guidosch/bikecounter/hardware/PCB/LogicLayer/BikeCounter_LogicLayer_v0.1_r1_p2.png

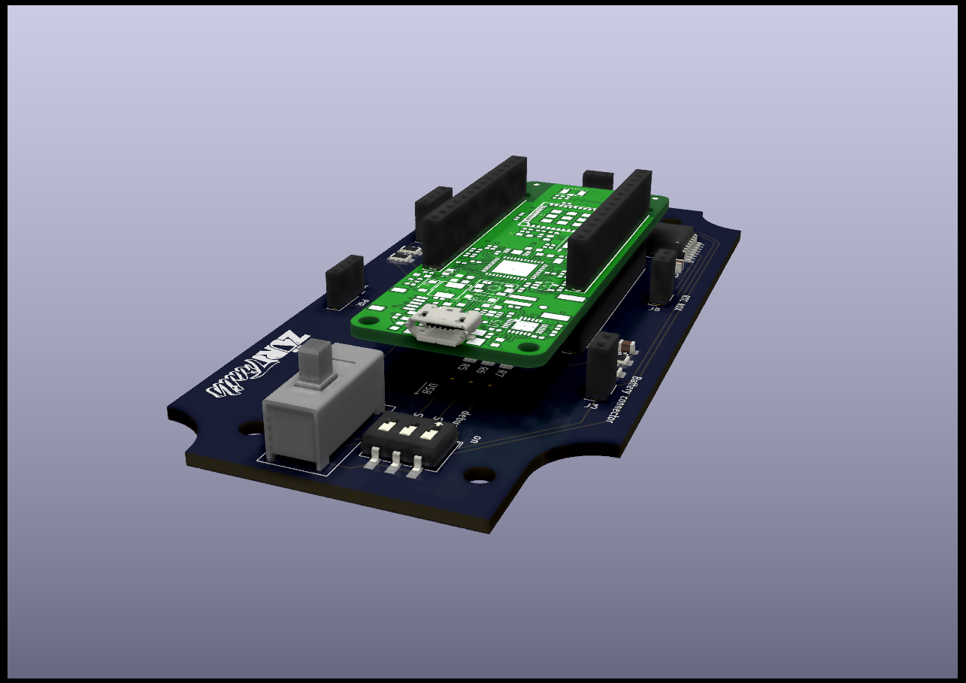
hardware/PCB/LogicLayer/BikeCounter_LogicLayer_v0.1_r1_p2.png
