guidosch/bikecounter/software/BikeCounterPro/src/timerSchedule/date.h

#ifndef DATE_H
#define DATE_H

// The MIT License (MIT)
//
// Copyright (c) 2015, 2016, 2017 Howard Hinnant
// Copyright (c) 2016 Adrian Colomitchi
// Copyright (c) 2017 Florian Dang
// Copyright (c) 2017 Paul Thompson
// Copyright (c) 2018, 2019 Tomasz Kamiński
// Copyright (c) 2019 Jiangang Zhuang
//
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
// Our apologies.  When the previous paragraph was written, lowercase had not yet
// been invented (that would involve another several millennia of evolution).
// We did not mean to shout.

#ifndef HAS_STRING_VIEW
#  if __cplusplus >= 201703 || (defined(_MSVC_LANG) && _MSVC_LANG >= 201703L)
#    define HAS_STRING_VIEW 1
#  else
#    define HAS_STRING_VIEW 0
#  endif
#endif  // HAS_STRING_VIEW

#include <cassert>
#include <algorithm>
#include <cctype>
#include <chrono>
#include <climits>
#include <cmath>
#include <cstddef>
#include <cstdint>
#include <cstdlib>
#include <ctime>
#include <ios>
#include <istream>
#include <iterator>
#include <limits>
#include <locale>
#include <memory>
#include <ostream>
#include <ratio>
#include <sstream>
#include <stdexcept>
#include <string>
#if HAS_STRING_VIEW
# include <string_view>
#endif
#include <utility>
#include <type_traits>

#ifdef __GNUC__
# pragma GCC diagnostic push
# if __GNUC__ > 4 || (__GNUC__ == 4 && __GNUC_MINOR__ > 7)
#  pragma GCC diagnostic ignored "-Wpedantic"
# endif
# if __GNUC__ < 5
   // GCC 4.9 Bug 61489 Wrong warning with -Wmissing-field-initializers
#  pragma GCC diagnostic ignored "-Wmissing-field-initializers"
# endif
#endif

#ifdef _MSC_VER
#   pragma warning(push)
// warning C4127: conditional expression is constant
#   pragma warning(disable : 4127)
#endif

namespace date
{

    //---------------+
    // Configuration |
    //---------------+

#ifndef ONLY_C_LOCALE
#  define ONLY_C_LOCALE 0
#endif

#if defined(_MSC_VER) && (!defined(__clang__) || (_MSC_VER < 1910))
// MSVC
#  ifndef _SILENCE_CXX17_UNCAUGHT_EXCEPTION_DEPRECATION_WARNING
#    define _SILENCE_CXX17_UNCAUGHT_EXCEPTION_DEPRECATION_WARNING
#  endif
#  if _MSC_VER < 1910
//   before VS2017
#    define CONSTDATA const
#    define CONSTCD11
#    define CONSTCD14
#    define NOEXCEPT _NOEXCEPT
#  else
//   VS2017 and later
#    define CONSTDATA constexpr const
#    define CONSTCD11 constexpr
#    define CONSTCD14 constexpr
#    define NOEXCEPT noexcept
#  endif

#elif defined(__SUNPRO_CC) && __SUNPRO_CC <= 0x5150
// Oracle Developer Studio 12.6 and earlier
#  define CONSTDATA constexpr const
#  define CONSTCD11 constexpr
#  define CONSTCD14
#  define NOEXCEPT noexcept

#elif __cplusplus >= 201402
// C++14
#  define CONSTDATA constexpr const
#  define CONSTCD11 constexpr
#  define CONSTCD14 constexpr
#  define NOEXCEPT noexcept
#else
// C++11
#  define CONSTDATA constexpr const
#  define CONSTCD11 constexpr
#  define CONSTCD14
#  define NOEXCEPT noexcept
#endif

#ifndef HAS_UNCAUGHT_EXCEPTIONS
#  if __cplusplus >= 201703 || (defined(_MSVC_LANG) && _MSVC_LANG >= 201703L)
#    define HAS_UNCAUGHT_EXCEPTIONS 1
#  else
#    define HAS_UNCAUGHT_EXCEPTIONS 0
#  endif
#endif  // HAS_UNCAUGHT_EXCEPTIONS

#ifndef HAS_VOID_T
#  if __cplusplus >= 201703 || (defined(_MSVC_LANG) && _MSVC_LANG >= 201703L)
#    define HAS_VOID_T 1
#  else
#    define HAS_VOID_T 0
#  endif
#endif  // HAS_VOID_T

// Protect from Oracle sun macro
#ifdef sun
#  undef sun
#endif

// Work around for a NVCC compiler bug which causes it to fail
// to compile std::ratio_{multiply,divide} when used directly
// in the std::chrono::duration template instantiations below
    namespace detail {
        template <typename R1, typename R2>
        using ratio_multiply = decltype(std::ratio_multiply<R1, R2>{});

        template <typename R1, typename R2>
        using ratio_divide = decltype(std::ratio_divide<R1, R2>{});
    }  // namespace detail

    //-----------+
    // Interface |
    //-----------+

    // durations

    using days = std::chrono::duration
        <int, detail::ratio_multiply<std::ratio<24>, std::chrono::hours::period>>;

    using weeks = std::chrono::duration
        <int, detail::ratio_multiply<std::ratio<7>, days::period>>;

    using years = std::chrono::duration
        <int, detail::ratio_multiply<std::ratio<146097, 400>, days::period>>;

    using months = std::chrono::duration
        <int, detail::ratio_divide<years::period, std::ratio<12>>>;

    // time_point

    template <class Duration>
    using sys_time = std::chrono::time_point<std::chrono::system_clock, Duration>;

    using sys_days = sys_time<days>;
    using sys_seconds = sys_time<std::chrono::seconds>;

    struct local_t {};

    template <class Duration>
    using local_time = std::chrono::time_point<local_t, Duration>;

    using local_seconds = local_time<std::chrono::seconds>;
    using local_days = local_time<days>;

    // types

    struct last_spec
    {
        explicit last_spec() = default;
    };

    class day;
    class month;
    class year;

    class weekday;
    class weekday_indexed;
    class weekday_last;

    class month_day;
    class month_day_last;
    class month_weekday;
    class month_weekday_last;

    class year_month;

    class year_month_day;
    class year_month_day_last;
    class year_month_weekday;
    class year_month_weekday_last;

    // date composition operators

    CONSTCD11 year_month operator/(const year& y, const month& m) NOEXCEPT;
    CONSTCD11 year_month operator/(const year& y, int          m) NOEXCEPT;

    CONSTCD11 month_day operator/(const day& d, const month& m) NOEXCEPT;
    CONSTCD11 month_day operator/(const day& d, int          m) NOEXCEPT;
    CONSTCD11 month_day operator/(const month& m, const day& d) NOEXCEPT;
    CONSTCD11 month_day operator/(const month& m, int        d) NOEXCEPT;
    CONSTCD11 month_day operator/(int          m, const day& d) NOEXCEPT;

    CONSTCD11 month_day_last operator/(const month& m, last_spec) NOEXCEPT;
    CONSTCD11 month_day_last operator/(int          m, last_spec) NOEXCEPT;
    CONSTCD11 month_day_last operator/(last_spec, const month& m) NOEXCEPT;
    CONSTCD11 month_day_last operator/(last_spec, int          m) NOEXCEPT;

    CONSTCD11 month_weekday operator/(const month& m, const weekday_indexed& wdi) NOEXCEPT;
    CONSTCD11 month_weekday operator/(int          m, const weekday_indexed& wdi) NOEXCEPT;
    CONSTCD11 month_weekday operator/(const weekday_indexed& wdi, const month& m) NOEXCEPT;
    CONSTCD11 month_weekday operator/(const weekday_indexed& wdi, int          m) NOEXCEPT;

    CONSTCD11 month_weekday_last operator/(const month& m, const weekday_last& wdl) NOEXCEPT;
    CONSTCD11 month_weekday_last operator/(int          m, const weekday_last& wdl) NOEXCEPT;
    CONSTCD11 month_weekday_last operator/(const weekday_last& wdl, const month& m) NOEXCEPT;
    CONSTCD11 month_weekday_last operator/(const weekday_last& wdl, int          m) NOEXCEPT;

    CONSTCD11 year_month_day operator/(const year_month& ym, const day& d) NOEXCEPT;
    CONSTCD11 year_month_day operator/(const year_month& ym, int        d) NOEXCEPT;
    CONSTCD11 year_month_day operator/(const year& y, const month_day& md) NOEXCEPT;
    CONSTCD11 year_month_day operator/(int         y, const month_day& md) NOEXCEPT;
    CONSTCD11 year_month_day operator/(const month_day& md, const year& y) NOEXCEPT;
    CONSTCD11 year_month_day operator/(const month_day& md, int         y) NOEXCEPT;

    CONSTCD11
        year_month_day_last operator/(const year_month& ym, last_spec) NOEXCEPT;
    CONSTCD11
        year_month_day_last operator/(const year& y, const month_day_last& mdl) NOEXCEPT;
    CONSTCD11
        year_month_day_last operator/(int         y, const month_day_last& mdl) NOEXCEPT;
    CONSTCD11
        year_month_day_last operator/(const month_day_last& mdl, const year& y) NOEXCEPT;
    CONSTCD11
        year_month_day_last operator/(const month_day_last& mdl, int         y) NOEXCEPT;

    CONSTCD11
        year_month_weekday
        operator/(const year_month& ym, const weekday_indexed& wdi) NOEXCEPT;

    CONSTCD11
        year_month_weekday
        operator/(const year& y, const month_weekday& mwd) NOEXCEPT;

    CONSTCD11
        year_month_weekday
        operator/(int                y, const month_weekday& mwd) NOEXCEPT;

    CONSTCD11
        year_month_weekday
        operator/(const month_weekday& mwd, const year& y) NOEXCEPT;

    CONSTCD11
        year_month_weekday
        operator/(const month_weekday& mwd, int                  y) NOEXCEPT;

    CONSTCD11
        year_month_weekday_last
        operator/(const year_month& ym, const weekday_last& wdl) NOEXCEPT;

    CONSTCD11
        year_month_weekday_last
        operator/(const year& y, const month_weekday_last& mwdl) NOEXCEPT;

    CONSTCD11
        year_month_weekday_last
        operator/(int         y, const month_weekday_last& mwdl) NOEXCEPT;

    CONSTCD11
        year_month_weekday_last
        operator/(const month_weekday_last& mwdl, const year& y) NOEXCEPT;

    CONSTCD11
        year_month_weekday_last
        operator/(const month_weekday_last& mwdl, int         y) NOEXCEPT;

    // Detailed interface

    // day

    class day
    {
        unsigned char d_;

    public:
        day() = default;
        explicit CONSTCD11 day(unsigned d) NOEXCEPT;

        CONSTCD14 day& operator++()    NOEXCEPT;
        CONSTCD14 day  operator++(int) NOEXCEPT;
        CONSTCD14 day& operator--()    NOEXCEPT;
        CONSTCD14 day  operator--(int) NOEXCEPT;

        CONSTCD14 day& operator+=(const days& d) NOEXCEPT;
        CONSTCD14 day& operator-=(const days& d) NOEXCEPT;

        CONSTCD11 explicit operator unsigned() const NOEXCEPT;
        CONSTCD11 bool ok() const NOEXCEPT;
    };

    CONSTCD11 bool operator==(const day& x, const day& y) NOEXCEPT;
    CONSTCD11 bool operator!=(const day& x, const day& y) NOEXCEPT;
    CONSTCD11 bool operator< (const day& x, const day& y) NOEXCEPT;
    CONSTCD11 bool operator> (const day& x, const day& y) NOEXCEPT;
    CONSTCD11 bool operator<=(const day& x, const day& y) NOEXCEPT;
    CONSTCD11 bool operator>=(const day& x, const day& y) NOEXCEPT;

    CONSTCD11 day  operator+(const day& x, const days& y) NOEXCEPT;
    CONSTCD11 day  operator+(const days& x, const day& y) NOEXCEPT;
    CONSTCD11 day  operator-(const day& x, const days& y) NOEXCEPT;
    CONSTCD11 days operator-(const day& x, const day& y) NOEXCEPT;

    template<class CharT, class Traits>
    std::basic_ostream<CharT, Traits>&
        operator<<(std::basic_ostream<CharT, Traits>& os, const day& d);

    // month

    class month
    {
        unsigned char m_;

    public:
        month() = default;
        explicit CONSTCD11 month(unsigned m) NOEXCEPT;

        CONSTCD14 month& operator++()    NOEXCEPT;
        CONSTCD14 month  operator++(int) NOEXCEPT;
        CONSTCD14 month& operator--()    NOEXCEPT;
        CONSTCD14 month  operator--(int) NOEXCEPT;

        CONSTCD14 month& operator+=(const months& m) NOEXCEPT;
        CONSTCD14 month& operator-=(const months& m) NOEXCEPT;

        CONSTCD11 explicit operator unsigned() const NOEXCEPT;
        CONSTCD11 bool ok() const NOEXCEPT;
    };

    CONSTCD11 bool operator==(const month& x, const month& y) NOEXCEPT;
    CONSTCD11 bool operator!=(const month& x, const month& y) NOEXCEPT;
    CONSTCD11 bool operator< (const month& x, const month& y) NOEXCEPT;
    CONSTCD11 bool operator> (const month& x, const month& y) NOEXCEPT;
    CONSTCD11 bool operator<=(const month& x, const month& y) NOEXCEPT;
    CONSTCD11 bool operator>=(const month& x, const month& y) NOEXCEPT;

    CONSTCD14 month  operator+(const month& x, const months& y) NOEXCEPT;
    CONSTCD14 month  operator+(const months& x, const month& y) NOEXCEPT;
    CONSTCD14 month  operator-(const month& x, const months& y) NOEXCEPT;
    CONSTCD14 months operator-(const month& x, const month& y) NOEXCEPT;

    template<class CharT, class Traits>
    std::basic_ostream<CharT, Traits>&
        operator<<(std::basic_ostream<CharT, Traits>& os, const month& m);

    // year

    class year
    {
        short y_;

    public:
        year() = default;
        explicit CONSTCD11 year(int y) NOEXCEPT;

        CONSTCD14 year& operator++()    NOEXCEPT;
        CONSTCD14 year  operator++(int) NOEXCEPT;
        CONSTCD14 year& operator--()    NOEXCEPT;
        CONSTCD14 year  operator--(int) NOEXCEPT;

        CONSTCD14 year& operator+=(const years& y) NOEXCEPT;
        CONSTCD14 year& operator-=(const years& y) NOEXCEPT;

        CONSTCD11 year operator-() const NOEXCEPT;
        CONSTCD11 year operator+() const NOEXCEPT;

        CONSTCD11 bool is_leap() const NOEXCEPT;

        CONSTCD11 explicit operator int() const NOEXCEPT;
        CONSTCD11 bool ok() const NOEXCEPT;

        static CONSTCD11 year min() NOEXCEPT { return year{ -32767 }; }
        static CONSTCD11 year max() NOEXCEPT { return year{ 32767 }; }
    };

    CONSTCD11 bool operator==(const year& x, const year& y) NOEXCEPT;
    CONSTCD11 bool operator!=(const year& x, const year& y) NOEXCEPT;
    CONSTCD11 bool operator< (const year& x, const year& y) NOEXCEPT;
    CONSTCD11 bool operator> (const year& x, const year& y) NOEXCEPT;
    CONSTCD11 bool operator<=(const year& x, const year& y) NOEXCEPT;
    CONSTCD11 bool operator>=(const year& x, const year& y) NOEXCEPT;

    CONSTCD11 year  operator+(const year& x, const years& y) NOEXCEPT;
    CONSTCD11 year  operator+(const years& x, const year& y) NOEXCEPT;
    CONSTCD11 year  operator-(const year& x, const years& y) NOEXCEPT;
    CONSTCD11 years operator-(const year& x, const year& y) NOEXCEPT;

    template<class CharT, class Traits>
    std::basic_ostream<CharT, Traits>&
        operator<<(std::basic_ostream<CharT, Traits>& os, const year& y);

    // weekday

    class weekday
    {
        unsigned char wd_;
    public:
        weekday() = default;
        explicit CONSTCD11 weekday(unsigned wd) NOEXCEPT;
        CONSTCD14 weekday(const sys_days& dp) NOEXCEPT;
        CONSTCD14 explicit weekday(const local_days& dp) NOEXCEPT;

        CONSTCD14 weekday& operator++()    NOEXCEPT;
        CONSTCD14 weekday  operator++(int) NOEXCEPT;
        CONSTCD14 weekday& operator--()    NOEXCEPT;
        CONSTCD14 weekday  operator--(int) NOEXCEPT;

        CONSTCD14 weekday& operator+=(const days& d) NOEXCEPT;
        CONSTCD14 weekday& operator-=(const days& d) NOEXCEPT;

        CONSTCD11 bool ok() const NOEXCEPT;

        CONSTCD11 unsigned c_encoding() const NOEXCEPT;
        CONSTCD11 unsigned iso_encoding() const NOEXCEPT;

        CONSTCD11 weekday_indexed operator[](unsigned index) const NOEXCEPT;
        CONSTCD11 weekday_last    operator[](last_spec)      const NOEXCEPT;

    private:
        static CONSTCD14 unsigned char weekday_from_days(int z) NOEXCEPT;

        friend CONSTCD11 bool operator==(const weekday& x, const weekday& y) NOEXCEPT;
        friend CONSTCD14 days operator-(const weekday& x, const weekday& y) NOEXCEPT;
        friend CONSTCD14 weekday operator+(const weekday& x, const days& y) NOEXCEPT;
        template<class CharT, class Traits>
        friend std::basic_ostream<CharT, Traits>&
            operator<<(std::basic_ostream<CharT, Traits>& os, const weekday& wd);
        friend class weekday_indexed;
    };

    CONSTCD11 bool operator==(const weekday& x, const weekday& y) NOEXCEPT;
    CONSTCD11 bool operator!=(const weekday& x, const weekday& y) NOEXCEPT;

    CONSTCD14 weekday operator+(const weekday& x, const days& y) NOEXCEPT;
    CONSTCD14 weekday operator+(const days& x, const weekday& y) NOEXCEPT;
    CONSTCD14 weekday operator-(const weekday& x, const days& y) NOEXCEPT;
    CONSTCD14 days    operator-(const weekday& x, const weekday& y) NOEXCEPT;

    template<class CharT, class Traits>
    std::basic_ostream<CharT, Traits>&
        operator<<(std::basic_ostream<CharT, Traits>& os, const weekday& wd);

    // weekday_indexed

    class weekday_indexed
    {
        unsigned char wd_ : 4;
        unsigned char index_ : 4;

    public:
        weekday_indexed() = default;
        CONSTCD11 weekday_indexed(const date::weekday& wd, unsigned index) NOEXCEPT;

        CONSTCD11 date::weekday weekday() const NOEXCEPT;
        CONSTCD11 unsigned index() const NOEXCEPT;
        CONSTCD11 bool ok() const NOEXCEPT;
    };

    CONSTCD11 bool operator==(const weekday_indexed& x, const weekday_indexed& y) NOEXCEPT;
    CONSTCD11 bool operator!=(const weekday_indexed& x, const weekday_indexed& y) NOEXCEPT;

    template<class CharT, class Traits>
    std::basic_ostream<CharT, Traits>&
        operator<<(std::basic_ostream<CharT, Traits>& os, const weekday_indexed& wdi);

    // weekday_last

    class weekday_last
    {
        date::weekday wd_;

    public:
        explicit CONSTCD11 weekday_last(const date::weekday& wd) NOEXCEPT;

        CONSTCD11 date::weekday weekday() const NOEXCEPT;
        CONSTCD11 bool ok() const NOEXCEPT;
    };

    CONSTCD11 bool operator==(const weekday_last& x, const weekday_last& y) NOEXCEPT;
    CONSTCD11 bool operator!=(const weekday_last& x, const weekday_last& y) NOEXCEPT;

    template<class CharT, class Traits>
    std::basic_ostream<CharT, Traits>&
        operator<<(std::basic_ostream<CharT, Traits>& os, const weekday_last& wdl);

    namespace detail
    {

        struct unspecified_month_disambiguator {};

    }  // namespace detail

    // year_month

    class year_month
    {
        date::year  y_;
        date::month m_;

    public:
        year_month() = default;
        CONSTCD11 year_month(const date::year& y, const date::month& m) NOEXCEPT;

        CONSTCD11 date::year  year()  const NOEXCEPT;
        CONSTCD11 date::month month() const NOEXCEPT;

        template<class = detail::unspecified_month_disambiguator>
        CONSTCD14 year_month& operator+=(const months& dm) NOEXCEPT;
        template<class = detail::unspecified_month_disambiguator>
        CONSTCD14 year_month& operator-=(const months& dm) NOEXCEPT;
        CONSTCD14 year_month& operator+=(const years& dy) NOEXCEPT;
        CONSTCD14 year_month& operator-=(const years& dy) NOEXCEPT;

        CONSTCD11 bool ok() const NOEXCEPT;
    };

    CONSTCD11 bool operator==(const year_month& x, const year_month& y) NOEXCEPT;
    CONSTCD11 bool operator!=(const year_month& x, const year_month& y) NOEXCEPT;
    CONSTCD11 bool operator< (const year_month& x, const year_month& y) NOEXCEPT;
    CONSTCD11 bool operator> (const year_month& x, const year_month& y) NOEXCEPT;
    CONSTCD11 bool operator<=(const year_month& x, const year_month& y) NOEXCEPT;
    CONSTCD11 bool operator>=(const year_month& x, const year_month& y) NOEXCEPT;

    template<class = detail::unspecified_month_disambiguator>
    CONSTCD14 year_month operator+(const year_month& ym, const months& dm) NOEXCEPT;
    template<class = detail::unspecified_month_disambiguator>
    CONSTCD14 year_month operator+(const months& dm, const year_month& ym) NOEXCEPT;
    template<class = detail::unspecified_month_disambiguator>
    CONSTCD14 year_month operator-(const year_month& ym, const months& dm) NOEXCEPT;

    CONSTCD11 months operator-(const year_month& x, const year_month& y) NOEXCEPT;
    CONSTCD11 year_month operator+(const year_month& ym, const years& dy) NOEXCEPT;
    CONSTCD11 year_month operator+(const years& dy, const year_month& ym) NOEXCEPT;
    CONSTCD11 year_month operator-(const year_month& ym, const years& dy) NOEXCEPT;

    template<class CharT, class Traits>
    std::basic_ostream<CharT, Traits>&
        operator<<(std::basic_ostream<CharT, Traits>& os, const year_month& ym);

    // month_day

    class month_day
    {
        date::month m_;
        date::day   d_;

    public:
        month_day() = default;
        CONSTCD11 month_day(const date::month& m, const date::day& d) NOEXCEPT;

        CONSTCD11 date::month month() const NOEXCEPT;
        CONSTCD11 date::day   day() const NOEXCEPT;

        CONSTCD14 bool ok() const NOEXCEPT;
    };

    CONSTCD11 bool operator==(const month_day& x, const month_day& y) NOEXCEPT;
    CONSTCD11 bool operator!=(const month_day& x, const month_day& y) NOEXCEPT;
    CONSTCD11 bool operator< (const month_day& x, const month_day& y) NOEXCEPT;
    CONSTCD11 bool operator> (const month_day& x, const month_day& y) NOEXCEPT;
    CONSTCD11 bool operator<=(const month_day& x, const month_day& y) NOEXCEPT;
    CONSTCD11 bool operator>=(const month_day& x, const month_day& y) NOEXCEPT;

    template<class CharT, class Traits>
    std::basic_ostream<CharT, Traits>&
        operator<<(std::basic_ostream<CharT, Traits>& os, const month_day& md);

    // month_day_last

    class month_day_last
    {
        date::month m_;

    public:
        CONSTCD11 explicit month_day_last(const date::month& m) NOEXCEPT;

        CONSTCD11 date::month month() const NOEXCEPT;
        CONSTCD11 bool ok() const NOEXCEPT;
    };

    CONSTCD11 bool operator==(const month_day_last& x, const month_day_last& y) NOEXCEPT;
    CONSTCD11 bool operator!=(const month_day_last& x, const month_day_last& y) NOEXCEPT;
    CONSTCD11 bool operator< (const month_day_last& x, const month_day_last& y) NOEXCEPT;
    CONSTCD11 bool operator> (const month_day_last& x, const month_day_last& y) NOEXCEPT;
    CONSTCD11 bool operator<=(const month_day_last& x, const month_day_last& y) NOEXCEPT;
    CONSTCD11 bool operator>=(const month_day_last& x, const month_day_last& y) NOEXCEPT;

    template<class CharT, class Traits>
    std::basic_ostream<CharT, Traits>&
        operator<<(std::basic_ostream<CharT, Traits>& os, const month_day_last& mdl);

    // month_weekday

    class month_weekday
    {
        date::month           m_;
        date::weekday_indexed wdi_;
    public:
        CONSTCD11 month_weekday(const date::month& m,
            const date::weekday_indexed& wdi) NOEXCEPT;

        CONSTCD11 date::month           month()           const NOEXCEPT;
        CONSTCD11 date::weekday_indexed weekday_indexed() const NOEXCEPT;

        CONSTCD11 bool ok() const NOEXCEPT;
    };

    CONSTCD11 bool operator==(const month_weekday& x, const month_weekday& y) NOEXCEPT;
    CONSTCD11 bool operator!=(const month_weekday& x, const month_weekday& y) NOEXCEPT;

    template<class CharT, class Traits>
    std::basic_ostream<CharT, Traits>&
        operator<<(std::basic_ostream<CharT, Traits>& os, const month_weekday& mwd);

    // month_weekday_last

    class month_weekday_last
    {
        date::month        m_;
        date::weekday_last wdl_;

    public:
        CONSTCD11 month_weekday_last(const date::month& m,
            const date::weekday_last& wd) NOEXCEPT;

        CONSTCD11 date::month        month()        const NOEXCEPT;
        CONSTCD11 date::weekday_last weekday_last() const NOEXCEPT;

        CONSTCD11 bool ok() const NOEXCEPT;
    };

    CONSTCD11
        bool operator==(const month_weekday_last& x, const month_weekday_last& y) NOEXCEPT;
    CONSTCD11
        bool operator!=(const month_weekday_last& x, const month_weekday_last& y) NOEXCEPT;

    template<class CharT, class Traits>
    std::basic_ostream<CharT, Traits>&
        operator<<(std::basic_ostream<CharT, Traits>& os, const month_weekday_last& mwdl);

    // class year_month_day

    class year_month_day
    {
        date::year  y_;
        date::month m_;
        date::day   d_;

    public:
        year_month_day() = default;
        CONSTCD11 year_month_day(const date::year& y, const date::month& m,
            const date::day& d) NOEXCEPT;
        CONSTCD14 year_month_day(const year_month_day_last& ymdl) NOEXCEPT;

        CONSTCD14 year_month_day(sys_days dp) NOEXCEPT;
        CONSTCD14 explicit year_month_day(local_days dp) NOEXCEPT;

        template<class = detail::unspecified_month_disambiguator>
        CONSTCD14 year_month_day& operator+=(const months& m) NOEXCEPT;
        template<class = detail::unspecified_month_disambiguator>
        CONSTCD14 year_month_day& operator-=(const months& m) NOEXCEPT;
        CONSTCD14 year_month_day& operator+=(const years& y)  NOEXCEPT;
        CONSTCD14 year_month_day& operator-=(const years& y)  NOEXCEPT;

        CONSTCD11 date::year  year()  const NOEXCEPT;
        CONSTCD11 date::month month() const NOEXCEPT;
        CONSTCD11 date::day   day()   const NOEXCEPT;

        CONSTCD14 operator sys_days() const NOEXCEPT;
        CONSTCD14 explicit operator local_days() const NOEXCEPT;
        CONSTCD14 bool ok() const NOEXCEPT;

    private:
        static CONSTCD14 year_month_day from_days(days dp) NOEXCEPT;
        CONSTCD14 days to_days() const NOEXCEPT;
    };

    CONSTCD11 bool operator==(const year_month_day& x, const year_month_day& y) NOEXCEPT;
    CONSTCD11 bool operator!=(const year_month_day& x, const year_month_day& y) NOEXCEPT;
    CONSTCD11 bool operator< (const year_month_day& x, const year_month_day& y) NOEXCEPT;
    CONSTCD11 bool operator> (const year_month_day& x, const year_month_day& y) NOEXCEPT;
    CONSTCD11 bool operator<=(const year_month_day& x, const year_month_day& y) NOEXCEPT;
    CONSTCD11 bool operator>=(const year_month_day& x, const year_month_day& y) NOEXCEPT;

    template<class = detail::unspecified_month_disambiguator>
    CONSTCD14 year_month_day operator+(const year_month_day& ymd, const months& dm) NOEXCEPT;
    template<class = detail::unspecified_month_disambiguator>
    CONSTCD14 year_month_day operator+(const months& dm, const year_month_day& ymd) NOEXCEPT;
    template<class = detail::unspecified_month_disambiguator>
    CONSTCD14 year_month_day operator-(const year_month_day& ymd, const months& dm) NOEXCEPT;
    CONSTCD11 year_month_day operator+(const year_month_day& ymd, const years& dy)  NOEXCEPT;
    CONSTCD11 year_month_day operator+(const years& dy, const year_month_day& ymd)  NOEXCEPT;
    CONSTCD11 year_month_day operator-(const year_month_day& ymd, const years& dy)  NOEXCEPT;

    template<class CharT, class Traits>
    std::basic_ostream<CharT, Traits>&
        operator<<(std::basic_ostream<CharT, Traits>& os, const year_month_day& ymd);

    // year_month_day_last

    class year_month_day_last
    {
        date::year           y_;
        date::month_day_last mdl_;

    public:
        CONSTCD11 year_month_day_last(const date::year& y,
            const date::month_day_last& mdl) NOEXCEPT;

        template<class = detail::unspecified_month_disambiguator>
        CONSTCD14 year_month_day_last& operator+=(const months& m) NOEXCEPT;
        template<class = detail::unspecified_month_disambiguator>
        CONSTCD14 year_month_day_last& operator-=(const months& m) NOEXCEPT;
        CONSTCD14 year_month_day_last& operator+=(const years& y)  NOEXCEPT;
        CONSTCD14 year_month_day_last& operator-=(const years& y)  NOEXCEPT;

        CONSTCD11 date::year           year()           const NOEXCEPT;
        CONSTCD11 date::month          month()          const NOEXCEPT;
        CONSTCD11 date::month_day_last month_day_last() const NOEXCEPT;
        CONSTCD14 date::day            day()            const NOEXCEPT;

        CONSTCD14 operator sys_days() const NOEXCEPT;
        CONSTCD14 explicit operator local_days() const NOEXCEPT;
        CONSTCD11 bool ok() const NOEXCEPT;
    };

    CONSTCD11
        bool operator==(const year_month_day_last& x, const year_month_day_last& y) NOEXCEPT;
    CONSTCD11
        bool operator!=(const year_month_day_last& x, const year_month_day_last& y) NOEXCEPT;
    CONSTCD11
        bool operator< (const year_month_day_last& x, const year_month_day_last& y) NOEXCEPT;
    CONSTCD11
        bool operator> (const year_month_day_last& x, const year_month_day_last& y) NOEXCEPT;
    CONSTCD11
        bool operator<=(const year_month_day_last& x, const year_month_day_last& y) NOEXCEPT;
    CONSTCD11
        bool operator>=(const year_month_day_last& x, const year_month_day_last& y) NOEXCEPT;

    template<class = detail::unspecified_month_disambiguator>
    CONSTCD14
        year_month_day_last
        operator+(const year_month_day_last& ymdl, const months& dm) NOEXCEPT;

    template<class = detail::unspecified_month_disambiguator>
    CONSTCD14
        year_month_day_last
        operator+(const months& dm, const year_month_day_last& ymdl) NOEXCEPT;

    CONSTCD11
        year_month_day_last
        operator+(const year_month_day_last& ymdl, const years& dy) NOEXCEPT;

    CONSTCD11
        year_month_day_last
        operator+(const years& dy, const year_month_day_last& ymdl) NOEXCEPT;

    template<class = detail::unspecified_month_disambiguator>
    CONSTCD14
        year_month_day_last
        operator-(const year_month_day_last& ymdl, const months& dm) NOEXCEPT;

    CONSTCD11
        year_month_day_last
        operator-(const year_month_day_last& ymdl, const years& dy) NOEXCEPT;

    template<class CharT, class Traits>
    std::basic_ostream<CharT, Traits>&
        operator<<(std::basic_ostream<CharT, Traits>& os, const year_month_day_last& ymdl);

    // year_month_weekday

    class year_month_weekday
    {
        date::year            y_;
        date::month           m_;
        date::weekday_indexed wdi_;

    public:
        year_month_weekday() = default;
        CONSTCD11 year_month_weekday(const date::year& y, const date::month& m,
            const date::weekday_indexed& wdi) NOEXCEPT;
        CONSTCD14 year_month_weekday(const sys_days& dp) NOEXCEPT;
        CONSTCD14 explicit year_month_weekday(const local_days& dp) NOEXCEPT;

        template<class = detail::unspecified_month_disambiguator>
        CONSTCD14 year_month_weekday& operator+=(const months& m) NOEXCEPT;
        template<class = detail::unspecified_month_disambiguator>
        CONSTCD14 year_month_weekday& operator-=(const months& m) NOEXCEPT;
        CONSTCD14 year_month_weekday& operator+=(const years& y)  NOEXCEPT;
        CONSTCD14 year_month_weekday& operator-=(const years& y)  NOEXCEPT;

        CONSTCD11 date::year year() const NOEXCEPT;
        CONSTCD11 date::month month() const NOEXCEPT;
        CONSTCD11 date::weekday weekday() const NOEXCEPT;
        CONSTCD11 unsigned index() const NOEXCEPT;
        CONSTCD11 date::weekday_indexed weekday_indexed() const NOEXCEPT;

        CONSTCD14 operator sys_days() const NOEXCEPT;
        CONSTCD14 explicit operator local_days() const NOEXCEPT;
        CONSTCD14 bool ok() const NOEXCEPT;

    private:
        static CONSTCD14 year_month_weekday from_days(days dp) NOEXCEPT;
        CONSTCD14 days to_days() const NOEXCEPT;
    };

    CONSTCD11
        bool operator==(const year_month_weekday& x, const year_month_weekday& y) NOEXCEPT;
    CONSTCD11
        bool operator!=(const year_month_weekday& x, const year_month_weekday& y) NOEXCEPT;

    template<class = detail::unspecified_month_disambiguator>
    CONSTCD14
        year_month_weekday
        operator+(const year_month_weekday& ymwd, const months& dm) NOEXCEPT;

    template<class = detail::unspecified_month_disambiguator>
    CONSTCD14
        year_month_weekday
        operator+(const months& dm, const year_month_weekday& ymwd) NOEXCEPT;

    CONSTCD11
        year_month_weekday
        operator+(const year_month_weekday& ymwd, const years& dy) NOEXCEPT;

    CONSTCD11
        year_month_weekday
        operator+(const years& dy, const year_month_weekday& ymwd) NOEXCEPT;

    template<class = detail::unspecified_month_disambiguator>
    CONSTCD14
        year_month_weekday
        operator-(const year_month_weekday& ymwd, const months& dm) NOEXCEPT;

    CONSTCD11
        year_month_weekday
        operator-(const year_month_weekday& ymwd, const years& dy) NOEXCEPT;

    template<class CharT, class Traits>
    std::basic_ostream<CharT, Traits>&
        operator<<(std::basic_ostream<CharT, Traits>& os, const year_month_weekday& ymwdi);

    // year_month_weekday_last

    class year_month_weekday_last
    {
        date::year y_;
        date::month m_;
        date::weekday_last wdl_;

    public:
        CONSTCD11 year_month_weekday_last(const date::year& y, const date::month& m,
            const date::weekday_last& wdl) NOEXCEPT;

        template<class = detail::unspecified_month_disambiguator>
        CONSTCD14 year_month_weekday_last& operator+=(const months& m) NOEXCEPT;
        template<class = detail::unspecified_month_disambiguator>
        CONSTCD14 year_month_weekday_last& operator-=(const months& m) NOEXCEPT;
        CONSTCD14 year_month_weekday_last& operator+=(const years& y) NOEXCEPT;
        CONSTCD14 year_month_weekday_last& operator-=(const years& y) NOEXCEPT;

        CONSTCD11 date::year year() const NOEXCEPT;
        CONSTCD11 date::month month() const NOEXCEPT;
        CONSTCD11 date::weekday weekday() const NOEXCEPT;
        CONSTCD11 date::weekday_last weekday_last() const NOEXCEPT;

        CONSTCD14 operator sys_days() const NOEXCEPT;
        CONSTCD14 explicit operator local_days() const NOEXCEPT;
        CONSTCD11 bool ok() const NOEXCEPT;

    private:
        CONSTCD14 days to_days() const NOEXCEPT;
    };

    CONSTCD11
        bool
        operator==(const year_month_weekday_last& x, const year_month_weekday_last& y) NOEXCEPT;

    CONSTCD11
        bool
        operator!=(const year_month_weekday_last& x, const year_month_weekday_last& y) NOEXCEPT;

    template<class = detail::unspecified_month_disambiguator>
    CONSTCD14
        year_month_weekday_last
        operator+(const year_month_weekday_last& ymwdl, const months& dm) NOEXCEPT;

    template<class = detail::unspecified_month_disambiguator>
    CONSTCD14
        year_month_weekday_last
        operator+(const months& dm, const year_month_weekday_last& ymwdl) NOEXCEPT;

    CONSTCD11
        year_month_weekday_last
        operator+(const year_month_weekday_last& ymwdl, const years& dy) NOEXCEPT;

    CONSTCD11
        year_month_weekday_last
        operator+(const years& dy, const year_month_weekday_last& ymwdl) NOEXCEPT;

    template<class = detail::unspecified_month_disambiguator>
    CONSTCD14
        year_month_weekday_last
        operator-(const year_month_weekday_last& ymwdl, const months& dm) NOEXCEPT;

    CONSTCD11
        year_month_weekday_last
        operator-(const year_month_weekday_last& ymwdl, const years& dy) NOEXCEPT;

    template<class CharT, class Traits>
    std::basic_ostream<CharT, Traits>&
        operator<<(std::basic_ostream<CharT, Traits>& os, const year_month_weekday_last& ymwdl);

#if !defined(_MSC_VER) || (_MSC_VER >= 1900)
    inline namespace literals
    {

        CONSTCD11 date::day  operator "" _d(unsigned long long d) NOEXCEPT;
        CONSTCD11 date::year operator "" _y(unsigned long long y) NOEXCEPT;

    }  // inline namespace literals
#endif // !defined(_MSC_VER) || (_MSC_VER >= 1900)

// CONSTDATA date::month January{1};
// CONSTDATA date::month February{2};
// CONSTDATA date::month March{3};
// CONSTDATA date::month April{4};
// CONSTDATA date::month May{5};
// CONSTDATA date::month June{6};
// CONSTDATA date::month July{7};
// CONSTDATA date::month August{8};
// CONSTDATA date::month September{9};
// CONSTDATA date::month October{10};
// CONSTDATA date::month November{11};
// CONSTDATA date::month December{12};
//
// CONSTDATA date::weekday Sunday{0u};
// CONSTDATA date::weekday Monday{1u};
// CONSTDATA date::weekday Tuesday{2u};
// CONSTDATA date::weekday Wednesday{3u};
// CONSTDATA date::weekday Thursday{4u};
// CONSTDATA date::weekday Friday{5u};
// CONSTDATA date::weekday Saturday{6u};

#if HAS_VOID_T

    template <class T, class = std::void_t<>>
    struct is_clock
        : std::false_type
    {};

    template <class T>
    struct is_clock<T, std::void_t<decltype(T::now()), typename T::rep, typename T::period,
        typename T::duration, typename T::time_point,
        decltype(T::is_steady)>>
        : std::true_type
    {};

    template<class T> inline constexpr bool is_clock_v = is_clock<T>::value;

#endif  // HAS_VOID_T

    //----------------+
    // Implementation |
    //----------------+

    // utilities
    namespace detail {

        template<class CharT, class Traits = std::char_traits<CharT>>
        class save_istream
        {
        protected:
            std::basic_ios<CharT, Traits>& is_;
            CharT fill_;
            std::ios::fmtflags flags_;
            std::streamsize precision_;
            std::streamsize width_;
            std::basic_ostream<CharT, Traits>* tie_;
            std::locale loc_;

        public:
            ~save_istream()
            {
                is_.fill(fill_);
                is_.flags(flags_);
                is_.precision(precision_);
                is_.width(width_);
                is_.imbue(loc_);
                is_.tie(tie_);
            }

            save_istream(const save_istream&) = delete;
            save_istream& operator=(const save_istream&) = delete;

            explicit save_istream(std::basic_ios<CharT, Traits>& is)
                : is_(is)
                , fill_(is.fill())
                , flags_(is.flags())
                , precision_(is.precision())
                , width_(is.width(0))
                , tie_(is.tie(nullptr))
                , loc_(is.getloc())
            {
                if (tie_ != nullptr)
                    tie_->flush();
            }
        };

        template<class CharT, class Traits = std::char_traits<CharT>>
        class save_ostream
            : private save_istream<CharT, Traits>
        {
        public:
            ~save_ostream()
            {
                if ((this->flags_ & std::ios::unitbuf) &&
#if HAS_UNCAUGHT_EXCEPTIONS
                    std::uncaught_exceptions() == 0 &&
#else
                    !std::uncaught_exception() &&
#endif
                    this->is_.good())
                    this->is_.rdbuf()->pubsync();
            }

            save_ostream(const save_ostream&) = delete;
            save_ostream& operator=(const save_ostream&) = delete;

            explicit save_ostream(std::basic_ios<CharT, Traits>& os)
                : save_istream<CharT, Traits>(os)
            {
            }
        };

        template <class T>
        struct choose_trunc_type
        {
            static const int digits = std::numeric_limits<T>::digits;
            using type = typename std::conditional
                <
                digits < 32,
                std::int32_t,
                typename std::conditional
                <
                digits < 64,
                std::int64_t,
#ifdef __SIZEOF_INT128__
                __int128
#else
                std::int64_t
#endif
                >::type
                >::type;
        };

        template <class T>
        CONSTCD11
            inline
            typename std::enable_if
            <
            !std::chrono::treat_as_floating_point<T>::value,
            T
            >::type
            trunc(T t) NOEXCEPT
        {
            return t;
        }

        template <class T>
        CONSTCD14
            inline
            typename std::enable_if
            <
            std::chrono::treat_as_floating_point<T>::value,
            T
            >::type
            trunc(T t) NOEXCEPT
        {
            using std::numeric_limits;
            using I = typename choose_trunc_type<T>::type;
            CONSTDATA auto digits = numeric_limits<T>::digits;
            static_assert(digits < numeric_limits<I>::digits, "");
            CONSTDATA auto max = I{ 1 } << (digits - 1);
            CONSTDATA auto min = -max;
            const auto negative = t < T{ 0 };
            if (min <= t && t <= max && t != 0 && t == t)
            {
                t = static_cast<T>(static_cast<I>(t));
                if (t == 0 && negative)
                    t = -t;
            }
            return t;
        }

        template <std::intmax_t Xp, std::intmax_t Yp>
        struct static_gcd
        {
            static const std::intmax_t value = static_gcd<Yp, Xp% Yp>::value;
        };

        template <std::intmax_t Xp>
        struct static_gcd<Xp, 0>
        {
            static const std::intmax_t value = Xp;
        };

        template <>
        struct static_gcd<0, 0>
        {
            static const std::intmax_t value = 1;
        };

        template <class R1, class R2>
        struct no_overflow
        {
        private:
            static const std::intmax_t gcd_n1_n2 = static_gcd<R1::num, R2::num>::value;
            static const std::intmax_t gcd_d1_d2 = static_gcd<R1::den, R2::den>::value;
            static const std::intmax_t n1 = R1::num / gcd_n1_n2;
            static const std::intmax_t d1 = R1::den / gcd_d1_d2;
            static const std::intmax_t n2 = R2::num / gcd_n1_n2;
            static const std::intmax_t d2 = R2::den / gcd_d1_d2;
#ifdef __cpp_constexpr
            static const std::intmax_t max = std::numeric_limits<std::intmax_t>::max();
#else
            static const std::intmax_t max = LLONG_MAX;
#endif

            template <std::intmax_t Xp, std::intmax_t Yp, bool overflow>
            struct mul    // overflow == false
            {
                static const std::intmax_t value = Xp * Yp;
            };

            template <std::intmax_t Xp, std::intmax_t Yp>
            struct mul<Xp, Yp, true>
            {
                static const std::intmax_t value = 1;
            };

        public:
            static const bool value = (n1 <= max / d2) && (n2 <= max / d1);
            typedef std::ratio<mul<n1, d2, !value>::value,
                mul<n2, d1, !value>::value> type;
        };

    }  // detail

    // trunc towards zero
    template <class To, class Rep, class Period>
    CONSTCD11
        inline
        typename std::enable_if
        <
        detail::no_overflow<Period, typename To::period>::value,
        To
        >::type
        trunc(const std::chrono::duration<Rep, Period>& d)
    {
        return To{ detail::trunc(std::chrono::duration_cast<To>(d).count()) };
    }

    template <class To, class Rep, class Period>
    CONSTCD11
        inline
        typename std::enable_if
        <
        !detail::no_overflow<Period, typename To::period>::value,
        To
        >::type
        trunc(const std::chrono::duration<Rep, Period>& d)
    {
        using std::chrono::duration_cast;
        using std::chrono::duration;
        using rep = typename std::common_type<Rep, typename To::rep>::type;
        return To{ detail::trunc(duration_cast<To>(duration_cast<duration<rep>>(d)).count()) };
    }

#ifndef HAS_CHRONO_ROUNDING
#  if defined(_MSC_FULL_VER) && (_MSC_FULL_VER >= 190023918 || (_MSC_FULL_VER >= 190000000 && defined (__clang__)))
#    define HAS_CHRONO_ROUNDING 1
#  elif defined(__cpp_lib_chrono) && __cplusplus > 201402 && __cpp_lib_chrono >= 201510
#    define HAS_CHRONO_ROUNDING 1
#  elif defined(_LIBCPP_VERSION) && __cplusplus > 201402 && _LIBCPP_VERSION >= 3800
#    define HAS_CHRONO_ROUNDING 1
#  else
#    define HAS_CHRONO_ROUNDING 0
#  endif
#endif  // HAS_CHRONO_ROUNDING

#if HAS_CHRONO_ROUNDING == 0

    // round down
    template <class To, class Rep, class Period>
    CONSTCD14
        inline
        typename std::enable_if
        <
        detail::no_overflow<Period, typename To::period>::value,
        To
        >::type
        floor(const std::chrono::duration<Rep, Period>& d)
    {
        auto t = trunc<To>(d);
        if (t > d)
            return t - To{ 1 };
        return t;
    }

    template <class To, class Rep, class Period>
    CONSTCD14
        inline
        typename std::enable_if
        <
        !detail::no_overflow<Period, typename To::period>::value,
        To
        >::type
        floor(const std::chrono::duration<Rep, Period>& d)
    {
        using rep = typename std::common_type<Rep, typename To::rep>::type;
        return floor<To>(floor<std::chrono::duration<rep>>(d));
    }

    // round to nearest, to even on tie
    template <class To, class Rep, class Period>
    CONSTCD14
        inline
        To
        round(const std::chrono::duration<Rep, Period>& d)
    {
        auto t0 = floor<To>(d);
        auto t1 = t0 + To{ 1 };
        if (t1 == To{ 0 } && t0 < To{ 0 })
            t1 = -t1;
        auto diff0 = d - t0;
        auto diff1 = t1 - d;
        if (diff0 == diff1)
        {
            if (t0 - trunc<To>(t0 / 2) * 2 == To{ 0 })
                return t0;
            return t1;
        }
        if (diff0 < diff1)
            return t0;
        return t1;
    }

    // round up
    template <class To, class Rep, class Period>
    CONSTCD14
        inline
        To
        ceil(const std::chrono::duration<Rep, Period>& d)
    {
        auto t = trunc<To>(d);
        if (t < d)
            return t + To{ 1 };
        return t;
    }

    template <class Rep, class Period,
        class = typename std::enable_if
        <
        std::numeric_limits<Rep>::is_signed
    >::type>
        CONSTCD11
        std::chrono::duration<Rep, Period>
        date_abs(std::chrono::duration<Rep, Period> d)
    {
        return d >= d.zero() ? d : static_cast<decltype(d)>(-d);
    }

    // round down
    template <class To, class Clock, class FromDuration>
    CONSTCD11
        inline
        std::chrono::time_point<Clock, To>
        floor(const std::chrono::time_point<Clock, FromDuration>& tp)
    {
        using std::chrono::time_point;
        return time_point<Clock, To>{date::floor<To>(tp.time_since_epoch())};
    }

    // round to nearest, to even on tie
    template <class To, class Clock, class FromDuration>
    CONSTCD11
        inline
        std::chrono::time_point<Clock, To>
        round(const std::chrono::time_point<Clock, FromDuration>& tp)
    {
        using std::chrono::time_point;
        return time_point<Clock, To>{round<To>(tp.time_since_epoch())};
    }

    // round up
    template <class To, class Clock, class FromDuration>
    CONSTCD11
        inline
        std::chrono::time_point<Clock, To>
        ceil(const std::chrono::time_point<Clock, FromDuration>& tp)
    {
        using std::chrono::time_point;
        return time_point<Clock, To>{ceil<To>(tp.time_since_epoch())};
    }

#else  // HAS_CHRONO_ROUNDING == 1

    using std::chrono::floor;
    using std::chrono::ceil;
    using std::chrono::round;
    using std::chrono::abs;

#endif  // HAS_CHRONO_ROUNDING

    namespace detail
    {

        template <class To, class Rep, class Period>
        CONSTCD14
            inline
            typename std::enable_if
            <
            !std::chrono::treat_as_floating_point<typename To::rep>::value,
            To
            >::type
            round_i(const std::chrono::duration<Rep, Period>& d)
        {
            return round<To>(d);
        }

        template <class To, class Rep, class Period>
        CONSTCD14
            inline
            typename std::enable_if
            <
            std::chrono::treat_as_floating_point<typename To::rep>::value,
            To
            >::type
            round_i(const std::chrono::duration<Rep, Period>& d)
        {
            return d;
        }

        template <class To, class Clock, class FromDuration>
        CONSTCD11
            inline
            std::chrono::time_point<Clock, To>
            round_i(const std::chrono::time_point<Clock, FromDuration>& tp)
        {
            using std::chrono::time_point;
            return time_point<Clock, To>{round_i<To>(tp.time_since_epoch())};
        }

    }  // detail

    // trunc towards zero
    template <class To, class Clock, class FromDuration>
    CONSTCD11
        inline
        std::chrono::time_point<Clock, To>
        trunc(const std::chrono::time_point<Clock, FromDuration>& tp)
    {
        using std::chrono::time_point;
        return time_point<Clock, To>{trunc<To>(tp.time_since_epoch())};
    }

    // day

    CONSTCD11 inline day::day(unsigned d) NOEXCEPT : d_(static_cast<decltype(d_)>(d)) {}
    CONSTCD14 inline day& day::operator++() NOEXCEPT { ++d_; return *this; }
    CONSTCD14 inline day day::operator++(int) NOEXCEPT { auto tmp(*this); ++(*this); return tmp; }
    CONSTCD14 inline day& day::operator--() NOEXCEPT { --d_; return *this; }
    CONSTCD14 inline day day::operator--(int) NOEXCEPT { auto tmp(*this); --(*this); return tmp; }
    CONSTCD14 inline day& day::operator+=(const days& d) NOEXCEPT { *this = *this + d; return *this; }
    CONSTCD14 inline day& day::operator-=(const days& d) NOEXCEPT { *this = *this - d; return *this; }
    CONSTCD11 inline day::operator unsigned() const NOEXCEPT { return d_; }
    CONSTCD11 inline bool day::ok() const NOEXCEPT { return 1 <= d_ && d_ <= 31; }

    CONSTCD11
        inline
        bool
        operator==(const day& x, const day& y) NOEXCEPT
    {
        return static_cast<unsigned>(x) == static_cast<unsigned>(y);
    }

    CONSTCD11
        inline
        bool
        operator!=(const day& x, const day& y) NOEXCEPT
    {
        return !(x == y);
    }

    CONSTCD11
        inline
        bool
        operator<(const day& x, const day& y) NOEXCEPT
    {
        return static_cast<unsigned>(x) < static_cast<unsigned>(y);
    }

    CONSTCD11
        inline
        bool
        operator>(const day& x, const day& y) NOEXCEPT
    {
        return y < x;
    }

    CONSTCD11
        inline
        bool
        operator<=(const day& x, const day& y) NOEXCEPT
    {
        return !(y < x);
    }

    CONSTCD11
        inline
        bool
        operator>=(const day& x, const day& y) NOEXCEPT
    {
        return !(x < y);
    }

    CONSTCD11
        inline
        days
        operator-(const day& x, const day& y) NOEXCEPT
    {
        return days{ static_cast<days::rep>(static_cast<unsigned>(x)
                                         - static_cast<unsigned>(y)) };
    }

    CONSTCD11
        inline
        day
        operator+(const day& x, const days& y) NOEXCEPT
    {
        return day{ static_cast<unsigned>(x) + static_cast<unsigned>(y.count()) };
    }

    CONSTCD11
        inline
        day
        operator+(const days& x, const day& y) NOEXCEPT
    {
        return y + x;
    }

    CONSTCD11
        inline
        day
        operator-(const day& x, const days& y) NOEXCEPT
    {
        return x + -y;
    }

    namespace detail
    {

        template<class CharT, class Traits>
        std::basic_ostream<CharT, Traits>&
            low_level_fmt(std::basic_ostream<CharT, Traits>& os, const day& d)
        {
            detail::save_ostream<CharT, Traits> _(os);
            os.fill('0');
            os.flags(std::ios::dec | std::ios::right);
            os.width(2);
            os << static_cast<unsigned>(d);
            return os;
        }

    }  // namespace detail

    template<class CharT, class Traits>
    inline
        std::basic_ostream<CharT, Traits>&
        operator<<(std::basic_ostream<CharT, Traits>& os, const day& d)
    {
        detail::low_level_fmt(os, d);
        if (!d.ok())
            os << " is not a valid day";
        return os;
    }

    // month

    CONSTCD11 inline month::month(unsigned m) NOEXCEPT : m_(static_cast<decltype(m_)>(m)) {}
    CONSTCD14 inline month& month::operator++() NOEXCEPT { *this += months{ 1 }; return *this; }
    CONSTCD14 inline month month::operator++(int) NOEXCEPT { auto tmp(*this); ++(*this); return tmp; }
    CONSTCD14 inline month& month::operator--() NOEXCEPT { *this -= months{ 1 }; return *this; }
    CONSTCD14 inline month month::operator--(int) NOEXCEPT { auto tmp(*this); --(*this); return tmp; }

    CONSTCD14
        inline
        month&
        month::operator+=(const months& m) NOEXCEPT
    {
        *this = *this + m;
        return *this;
    }

    CONSTCD14
        inline
        month&
        month::operator-=(const months& m) NOEXCEPT
    {
        *this = *this - m;
        return *this;
    }

    CONSTCD11 inline month::operator unsigned() const NOEXCEPT { return m_; }
    CONSTCD11 inline bool month::ok() const NOEXCEPT { return 1 <= m_ && m_ <= 12; }

    CONSTCD11
        inline
        bool
        operator==(const month& x, const month& y) NOEXCEPT
    {
        return static_cast<unsigned>(x) == static_cast<unsigned>(y);
    }

    CONSTCD11
        inline
        bool
        operator!=(const month& x, const month& y) NOEXCEPT
    {
        return !(x == y);
    }

    CONSTCD11
        inline
        bool
        operator<(const month& x, const month& y) NOEXCEPT
    {
        return static_cast<unsigned>(x) < static_cast<unsigned>(y);
    }

    CONSTCD11
        inline
        bool
        operator>(const month& x, const month& y) NOEXCEPT
    {
        return y < x;
    }

    CONSTCD11
        inline
        bool
        operator<=(const month& x, const month& y) NOEXCEPT
    {
        return !(y < x);
    }

    CONSTCD11
        inline
        bool
        operator>=(const month& x, const month& y) NOEXCEPT
    {
        return !(x < y);
    }

    CONSTCD14
        inline
        months
        operator-(const month& x, const month& y) NOEXCEPT
    {
        auto const d = static_cast<unsigned>(x) - static_cast<unsigned>(y);
        return months(d <= 11 ? d : d + 12);
    }

    CONSTCD14
        inline
        month
        operator+(const month& x, const months& y) NOEXCEPT
    {
        auto const mu = static_cast<long long>(static_cast<unsigned>(x)) + y.count() - 1;
        auto const yr = (mu >= 0 ? mu : mu - 11) / 12;
        return month{ static_cast<unsigned>(mu - yr * 12 + 1) };
    }

    CONSTCD14
        inline
        month
        operator+(const months& x, const month& y) NOEXCEPT
    {
        return y + x;
    }

    CONSTCD14
        inline
        month
        operator-(const month& x, const months& y) NOEXCEPT
    {
        return x + -y;
    }

    namespace detail
    {

        template<class CharT, class Traits>
        std::basic_ostream<CharT, Traits>&
            low_level_fmt(std::basic_ostream<CharT, Traits>& os, const month& m)
        {
            if (m.ok())
            {
                CharT fmt[] = { '%', 'b', 0 };
                os << format(os.getloc(), fmt, m);
            }
            else
                os << static_cast<unsigned>(m);
            return os;
        }

    }  // namespace detail

    template<class CharT, class Traits>
    inline
        std::basic_ostream<CharT, Traits>&
        operator<<(std::basic_ostream<CharT, Traits>& os, const month& m)
    {
        detail::low_level_fmt(os, m);
        if (!m.ok())
            os << " is not a valid month";
        return os;
    }

    // year

    CONSTCD11 inline year::year(int y) NOEXCEPT : y_(static_cast<decltype(y_)>(y)) {}
    CONSTCD14 inline year& year::operator++() NOEXCEPT { ++y_; return *this; }
    CONSTCD14 inline year year::operator++(int) NOEXCEPT { auto tmp(*this); ++(*this); return tmp; }
    CONSTCD14 inline year& year::operator--() NOEXCEPT { --y_; return *this; }
    CONSTCD14 inline year year::operator--(int) NOEXCEPT { auto tmp(*this); --(*this); return tmp; }
    CONSTCD14 inline year& year::operator+=(const years& y) NOEXCEPT { *this = *this + y; return *this; }
    CONSTCD14 inline year& year::operator-=(const years& y) NOEXCEPT { *this = *this - y; return *this; }
    CONSTCD11 inline year year::operator-() const NOEXCEPT { return year{ -y_ }; }
    CONSTCD11 inline year year::operator+() const NOEXCEPT { return *this; }

    CONSTCD11
        inline
        bool
        year::is_leap() const NOEXCEPT
    {
        return y_ % 4 == 0 && (y_ % 100 != 0 || y_ % 400 == 0);
    }

    CONSTCD11 inline year::operator int() const NOEXCEPT { return y_; }

    CONSTCD11
        inline
        bool
        year::ok() const NOEXCEPT
    {
        return y_ != std::numeric_limits<short>::min();
    }

    CONSTCD11
        inline
        bool
        operator==(const year& x, const year& y) NOEXCEPT
    {
        return static_cast<int>(x) == static_cast<int>(y);
    }

    CONSTCD11
        inline
        bool
        operator!=(const year& x, const year& y) NOEXCEPT
    {
        return !(x == y);
    }

    CONSTCD11
        inline
        bool
        operator<(const year& x, const year& y) NOEXCEPT
    {
        return static_cast<int>(x) < static_cast<int>(y);
    }

    CONSTCD11
        inline
        bool
        operator>(const year& x, const year& y) NOEXCEPT
    {
        return y < x;
    }

    CONSTCD11
        inline
        bool
        operator<=(const year& x, const year& y) NOEXCEPT
    {
        return !(y < x);
    }

    CONSTCD11
        inline
        bool
        operator>=(const year& x, const year& y) NOEXCEPT
    {
        return !(x < y);
    }

    CONSTCD11
        inline
        years
        operator-(const year& x, const year& y) NOEXCEPT
    {
        return years{ static_cast<int>(x) - static_cast<int>(y) };
    }

    CONSTCD11
        inline
        year
        operator+(const year& x, const years& y) NOEXCEPT
    {
        return year{ static_cast<int>(x) + y.count() };
    }

    CONSTCD11
        inline
        year
        operator+(const years& x, const year& y) NOEXCEPT
    {
        return y + x;
    }

    CONSTCD11
        inline
        year
        operator-(const year& x, const years& y) NOEXCEPT
    {
        return year{ static_cast<int>(x) - y.count() };
    }

    namespace detail
    {

        template<class CharT, class Traits>
        std::basic_ostream<CharT, Traits>&
            low_level_fmt(std::basic_ostream<CharT, Traits>& os, const year& y)
        {
            detail::save_ostream<CharT, Traits> _(os);
            os.fill('0');
            os.flags(std::ios::dec | std::ios::internal);
            os.width(4 + (y < year{ 0 }));
            os.imbue(std::locale::classic());
            os << static_cast<int>(y);
            return os;
        }

    }  // namespace detail

    template<class CharT, class Traits>
    inline
        std::basic_ostream<CharT, Traits>&
        operator<<(std::basic_ostream<CharT, Traits>& os, const year& y)
    {
        detail::low_level_fmt(os, y);
        if (!y.ok())
            os << " is not a valid year";
        return os;
    }

    // weekday

    CONSTCD14
        inline
        unsigned char
        weekday::weekday_from_days(int z) NOEXCEPT
    {
        auto u = static_cast<unsigned>(z);
        return static_cast<unsigned char>(z >= -4 ? (u + 4) % 7 : u % 7);
    }

    CONSTCD11
        inline
        weekday::weekday(unsigned wd) NOEXCEPT
        : wd_(static_cast<decltype(wd_)>(wd != 7 ? wd : 0))
    {}

    CONSTCD14
        inline
        weekday::weekday(const sys_days& dp) NOEXCEPT
        : wd_(weekday_from_days(dp.time_since_epoch().count()))
    {}

    CONSTCD14
        inline
        weekday::weekday(const local_days& dp) NOEXCEPT
        : wd_(weekday_from_days(dp.time_since_epoch().count()))
    {}

    CONSTCD14 inline weekday& weekday::operator++() NOEXCEPT { *this += days{ 1 }; return *this; }
    CONSTCD14 inline weekday weekday::operator++(int) NOEXCEPT { auto tmp(*this); ++(*this); return tmp; }
    CONSTCD14 inline weekday& weekday::operator--() NOEXCEPT { *this -= days{ 1 }; return *this; }
    CONSTCD14 inline weekday weekday::operator--(int) NOEXCEPT { auto tmp(*this); --(*this); return tmp; }

    CONSTCD14
        inline
        weekday&
        weekday::operator+=(const days& d) NOEXCEPT
    {
        *this = *this + d;
        return *this;
    }

    CONSTCD14
        inline
        weekday&
        weekday::operator-=(const days& d) NOEXCEPT
    {
        *this = *this - d;
        return *this;
    }

    CONSTCD11 inline bool weekday::ok() const NOEXCEPT { return wd_ <= 6; }

    CONSTCD11
        inline
        unsigned weekday::c_encoding() const NOEXCEPT
    {
        return unsigned{ wd_ };
    }

    CONSTCD11
        inline
        unsigned weekday::iso_encoding() const NOEXCEPT
    {
        return unsigned{ ((wd_ == 0u) ? 7u : wd_) };
    }

    CONSTCD11
        inline
        bool
        operator==(const weekday& x, const weekday& y) NOEXCEPT
    {
        return x.wd_ == y.wd_;
    }

    CONSTCD11
        inline
        bool
        operator!=(const weekday& x, const weekday& y) NOEXCEPT
    {
        return !(x == y);
    }

    CONSTCD14
        inline
        days
        operator-(const weekday& x, const weekday& y) NOEXCEPT
    {
        auto const wdu = x.wd_ - y.wd_;
        auto const wk = (wdu >= 0 ? wdu : wdu - 6) / 7;
        return days{ wdu - wk * 7 };
    }

    CONSTCD14
        inline
        weekday
        operator+(const weekday& x, const days& y) NOEXCEPT
    {
        auto const wdu = static_cast<long long>(static_cast<unsigned>(x.wd_)) + y.count();
        auto const wk = (wdu >= 0 ? wdu : wdu - 6) / 7;
        return weekday{ static_cast<unsigned>(wdu - wk * 7) };
    }

    CONSTCD14
        inline
        weekday
        operator+(const days& x, const weekday& y) NOEXCEPT
    {
        return y + x;
    }

    CONSTCD14
        inline
        weekday
        operator-(const weekday& x, const days& y) NOEXCEPT
    {
        return x + -y;
    }

    namespace detail
    {

        template<class CharT, class Traits>
        std::basic_ostream<CharT, Traits>&
            low_level_fmt(std::basic_ostream<CharT, Traits>& os, const weekday& wd)
        {
            if (wd.ok())
            {
                CharT fmt[] = { '%', 'a', 0 };
                os << format(fmt, wd);
            }
            else
                os << wd.c_encoding();
            return os;
        }

    }  // namespace detail

    template<class CharT, class Traits>
    inline
        std::basic_ostream<CharT, Traits>&
        operator<<(std::basic_ostream<CharT, Traits>& os, const weekday& wd)
    {
        detail::low_level_fmt(os, wd);
        if (!wd.ok())
            os << " is not a valid weekday";
        return os;
    }

#if !defined(_MSC_VER) || (_MSC_VER >= 1900)
    inline namespace literals
    {

        CONSTCD11
            inline
            date::day
            operator "" _d(unsigned long long d) NOEXCEPT
        {
            return date::day{ static_cast<unsigned>(d) };
        }

        CONSTCD11
            inline
            date::year
            operator "" _y(unsigned long long y) NOEXCEPT
        {
            return date::year(static_cast<int>(y));
        }
#endif  // !defined(_MSC_VER) || (_MSC_VER >= 1900)

        CONSTDATA date::last_spec last{};

        CONSTDATA date::month jan{ 1 };
        CONSTDATA date::month feb{ 2 };
        CONSTDATA date::month mar{ 3 };
        CONSTDATA date::month apr{ 4 };
        CONSTDATA date::month may{ 5 };
        CONSTDATA date::month jun{ 6 };
        CONSTDATA date::month jul{ 7 };
        CONSTDATA date::month aug{ 8 };
        CONSTDATA date::month sep{ 9 };
        CONSTDATA date::month oct{ 10 };
        CONSTDATA date::month nov{ 11 };
        CONSTDATA date::month dec{ 12 };

        CONSTDATA date::weekday sun{ 0u };
        CONSTDATA date::weekday mon{ 1u };
        CONSTDATA date::weekday tue{ 2u };
        CONSTDATA date::weekday wed{ 3u };
        CONSTDATA date::weekday thu{ 4u };
        CONSTDATA date::weekday fri{ 5u };
        CONSTDATA date::weekday sat{ 6u };

#if !defined(_MSC_VER) || (_MSC_VER >= 1900)
    }  // inline namespace literals
#endif

    CONSTDATA date::month January{ 1 };
    CONSTDATA date::month February{ 2 };
    CONSTDATA date::month March{ 3 };
    CONSTDATA date::month April{ 4 };
    CONSTDATA date::month May{ 5 };
    CONSTDATA date::month June{ 6 };
    CONSTDATA date::month July{ 7 };
    CONSTDATA date::month August{ 8 };
    CONSTDATA date::month September{ 9 };
    CONSTDATA date::month October{ 10 };
    CONSTDATA date::month November{ 11 };
    CONSTDATA date::month December{ 12 };

    CONSTDATA date::weekday Monday{ 1 };
    CONSTDATA date::weekday Tuesday{ 2 };
    CONSTDATA date::weekday Wednesday{ 3 };
    CONSTDATA date::weekday Thursday{ 4 };
    CONSTDATA date::weekday Friday{ 5 };
    CONSTDATA date::weekday Saturday{ 6 };
    CONSTDATA date::weekday Sunday{ 7 };

    // weekday_indexed

    CONSTCD11
        inline
        weekday
        weekday_indexed::weekday() const NOEXCEPT
    {
        return date::weekday{ static_cast<unsigned>(wd_) };
    }

    CONSTCD11 inline unsigned weekday_indexed::index() const NOEXCEPT { return index_; }

    CONSTCD11
        inline
        bool
        weekday_indexed::ok() const NOEXCEPT
    {
        return weekday().ok() && 1 <= index_ && index_ <= 5;
    }

#ifdef __GNUC__
#  pragma GCC diagnostic push
#  pragma GCC diagnostic ignored "-Wconversion"
#endif  // __GNUC__

    CONSTCD11
        inline
        weekday_indexed::weekday_indexed(const date::weekday& wd, unsigned index) NOEXCEPT
        : wd_(static_cast<decltype(wd_)>(static_cast<unsigned>(wd.wd_)))
        , index_(static_cast<decltype(index_)>(index))
    {}

#ifdef __GNUC__
#  pragma GCC diagnostic pop
#endif  // __GNUC__

    namespace detail
    {

        template<class CharT, class Traits>
        std::basic_ostream<CharT, Traits>&
            low_level_fmt(std::basic_ostream<CharT, Traits>& os, const weekday_indexed& wdi)
        {
            return low_level_fmt(os, wdi.weekday()) << '[' << wdi.index() << ']';
        }

    }  // namespace detail

    template<class CharT, class Traits>
    inline
        std::basic_ostream<CharT, Traits>&
        operator<<(std::basic_ostream<CharT, Traits>& os, const weekday_indexed& wdi)
    {
        detail::low_level_fmt(os, wdi);
        if (!wdi.ok())
            os << " is not a valid weekday_indexed";
        return os;
    }

    CONSTCD11
        inline
        weekday_indexed
        weekday::operator[](unsigned index) const NOEXCEPT
    {
        return { *this, index };
    }

    CONSTCD11
        inline
        bool
        operator==(const weekday_indexed& x, const weekday_indexed& y) NOEXCEPT
    {
        return x.weekday() == y.weekday() && x.index() == y.index();
    }

    CONSTCD11
        inline
        bool
        operator!=(const weekday_indexed& x, const weekday_indexed& y) NOEXCEPT
    {
        return !(x == y);
    }

    // weekday_last

    CONSTCD11 inline date::weekday weekday_last::weekday() const NOEXCEPT { return wd_; }
    CONSTCD11 inline bool weekday_last::ok() const NOEXCEPT { return wd_.ok(); }
    CONSTCD11 inline weekday_last::weekday_last(const date::weekday& wd) NOEXCEPT : wd_(wd) {}

    CONSTCD11
        inline
        bool
        operator==(const weekday_last& x, const weekday_last& y) NOEXCEPT
    {
        return x.weekday() == y.weekday();
    }

    CONSTCD11
        inline
        bool
        operator!=(const weekday_last& x, const weekday_last& y) NOEXCEPT
    {
        return !(x == y);
    }

    namespace detail
    {

        template<class CharT, class Traits>
        std::basic_ostream<CharT, Traits>&
            low_level_fmt(std::basic_ostream<CharT, Traits>& os, const weekday_last& wdl)
        {
            return low_level_fmt(os, wdl.weekday()) << "[last]";
        }

    }  // namespace detail

    template<class CharT, class Traits>
    inline
        std::basic_ostream<CharT, Traits>&
        operator<<(std::basic_ostream<CharT, Traits>& os, const weekday_last& wdl)
    {
        detail::low_level_fmt(os, wdl);
        if (!wdl.ok())
            os << " is not a valid weekday_last";
        return os;
    }

    CONSTCD11
        inline
        weekday_last
        weekday::operator[](last_spec) const NOEXCEPT
    {
        return weekday_last{ *this };
    }

    // year_month

    CONSTCD11
        inline
        year_month::year_month(const date::year& y, const date::month& m) NOEXCEPT
        : y_(y)
        , m_(m)
    {}

    CONSTCD11 inline year year_month::year() const NOEXCEPT { return y_; }
    CONSTCD11 inline month year_month::month() const NOEXCEPT { return m_; }
    CONSTCD11 inline bool year_month::ok() const NOEXCEPT { return y_.ok() && m_.ok(); }

    template<class>
    CONSTCD14
        inline
        year_month&
        year_month::operator+=(const months& dm) NOEXCEPT
    {
        *this = *this + dm;
        return *this;
    }

    template<class>
    CONSTCD14
        inline
        year_month&
        year_month::operator-=(const months& dm) NOEXCEPT
    {
        *this = *this - dm;
        return *this;
    }

    CONSTCD14
        inline
        year_month&
        year_month::operator+=(const years& dy) NOEXCEPT
    {
        *this = *this + dy;
        return *this;
    }

    CONSTCD14
        inline
        year_month&
        year_month::operator-=(const years& dy) NOEXCEPT
    {
        *this = *this - dy;
        return *this;
    }

    CONSTCD11
        inline
        bool
        operator==(const year_month& x, const year_month& y) NOEXCEPT
    {
        return x.year() == y.year() && x.month() == y.month();
    }

    CONSTCD11
        inline
        bool
        operator!=(const year_month& x, const year_month& y) NOEXCEPT
    {
        return !(x == y);
    }

    CONSTCD11
        inline
        bool
        operator<(const year_month& x, const year_month& y) NOEXCEPT
    {
        return x.year() < y.year() ? true
            : (x.year() > y.year() ? false
                : (x.month() < y.month()));
    }

    CONSTCD11
        inline
        bool
        operator>(const year_month& x, const year_month& y) NOEXCEPT
    {
        return y < x;
    }

    CONSTCD11
        inline
        bool
        operator<=(const year_month& x, const year_month& y) NOEXCEPT
    {
        return !(y < x);
    }

    CONSTCD11
        inline
        bool
        operator>=(const year_month& x, const year_month& y) NOEXCEPT
    {
        return !(x < y);
    }

    template<class>
    CONSTCD14
        inline
        year_month
        operator+(const year_month& ym, const months& dm) NOEXCEPT
    {
        auto dmi = static_cast<int>(static_cast<unsigned>(ym.month())) - 1 + dm.count();
        auto dy = (dmi >= 0 ? dmi : dmi - 11) / 12;
        dmi = dmi - dy * 12 + 1;
        return (ym.year() + years(dy)) / month(static_cast<unsigned>(dmi));
    }

    template<class>
    CONSTCD14
        inline
        year_month
        operator+(const months& dm, const year_month& ym) NOEXCEPT
    {
        return ym + dm;
    }

    template<class>
    CONSTCD14
        inline
        year_month
        operator-(const year_month& ym, const months& dm) NOEXCEPT
    {
        return ym + -dm;
    }

    CONSTCD11
        inline
        months
        operator-(const year_month& x, const year_month& y) NOEXCEPT
    {
        return (x.year() - y.year()) +
            months(static_cast<unsigned>(x.month()) - static_cast<unsigned>(y.month()));
    }

    CONSTCD11
        inline
        year_month
        operator+(const year_month& ym, const years& dy) NOEXCEPT
    {
        return (ym.year() + dy) / ym.month();
    }

    CONSTCD11
        inline
        year_month
        operator+(const years& dy, const year_month& ym) NOEXCEPT
    {
        return ym + dy;
    }

    CONSTCD11
        inline
        year_month
        operator-(const year_month& ym, const years& dy) NOEXCEPT
    {
        return ym + -dy;
    }

    namespace detail
    {

        template<class CharT, class Traits>
        std::basic_ostream<CharT, Traits>&
            low_level_fmt(std::basic_ostream<CharT, Traits>& os, const year_month& ym)
        {
            low_level_fmt(os, ym.year()) << '/';
            return low_level_fmt(os, ym.month());
        }

    }  // namespace detail

    template<class CharT, class Traits>
    inline
        std::basic_ostream<CharT, Traits>&
        operator<<(std::basic_ostream<CharT, Traits>& os, const year_month& ym)
    {
        detail::low_level_fmt(os, ym);
        if (!ym.ok())
            os << " is not a valid year_month";
        return os;
    }

    // month_day

    CONSTCD11
        inline
        month_day::month_day(const date::month& m, const date::day& d) NOEXCEPT
        : m_(m)
        , d_(d)
    {}

    CONSTCD11 inline date::month month_day::month() const NOEXCEPT { return m_; }
    CONSTCD11 inline date::day month_day::day() const NOEXCEPT { return d_; }

    CONSTCD14
        inline
        bool
        month_day::ok() const NOEXCEPT
    {
        CONSTDATA date::day d[] =
        {
            date::day(31), date::day(29), date::day(31),
            date::day(30), date::day(31), date::day(30),
            date::day(31), date::day(31), date::day(30),
            date::day(31), date::day(30), date::day(31)
        };
        return m_.ok() && date::day{ 1 } <= d_ && d_ <= d[static_cast<unsigned>(m_) - 1];
    }

    CONSTCD11
        inline
        bool
        operator==(const month_day& x, const month_day& y) NOEXCEPT
    {
        return x.month() == y.month() && x.day() == y.day();
    }

    CONSTCD11
        inline
        bool
        operator!=(const month_day& x, const month_day& y) NOEXCEPT
    {
        return !(x == y);
    }

    CONSTCD11
        inline
        bool
        operator<(const month_day& x, const month_day& y) NOEXCEPT
    {
        return x.month() < y.month() ? true
            : (x.month() > y.month() ? false
                : (x.day() < y.day()));
    }

    CONSTCD11
        inline
        bool
        operator>(const month_day& x, const month_day& y) NOEXCEPT
    {
        return y < x;
    }

    CONSTCD11
        inline
        bool
        operator<=(const month_day& x, const month_day& y) NOEXCEPT
    {
        return !(y < x);
    }

    CONSTCD11
        inline
        bool
        operator>=(const month_day& x, const month_day& y) NOEXCEPT
    {
        return !(x < y);
    }

    namespace detail
    {

        template<class CharT, class Traits>
        std::basic_ostream<CharT, Traits>&
            low_level_fmt(std::basic_ostream<CharT, Traits>& os, const month_day& md)
        {
            low_level_fmt(os, md.month()) << '/';
            return low_level_fmt(os, md.day());
        }

    }  // namespace detail

    template<class CharT, class Traits>
    inline
        std::basic_ostream<CharT, Traits>&
        operator<<(std::basic_ostream<CharT, Traits>& os, const month_day& md)
    {
        detail::low_level_fmt(os, md);
        if (!md.ok())
            os << " is not a valid month_day";
        return os;
    }

    // month_day_last

    CONSTCD11 inline month month_day_last::month() const NOEXCEPT { return m_; }
    CONSTCD11 inline bool month_day_last::ok() const NOEXCEPT { return m_.ok(); }
    CONSTCD11 inline month_day_last::month_day_last(const date::month& m) NOEXCEPT : m_(m) {}

    CONSTCD11
        inline
        bool
        operator==(const month_day_last& x, const month_day_last& y) NOEXCEPT
    {
        return x.month() == y.month();
    }

    CONSTCD11
        inline
        bool
        operator!=(const month_day_last& x, const month_day_last& y) NOEXCEPT
    {
        return !(x == y);
    }

    CONSTCD11
        inline
        bool
        operator<(const month_day_last& x, const month_day_last& y) NOEXCEPT
    {
        return x.month() < y.month();
    }

    CONSTCD11
        inline
        bool
        operator>(const month_day_last& x, const month_day_last& y) NOEXCEPT
    {
        return y < x;
    }

    CONSTCD11
        inline
        bool
        operator<=(const month_day_last& x, const month_day_last& y) NOEXCEPT
    {
        return !(y < x);
    }

    CONSTCD11
        inline
        bool
        operator>=(const month_day_last& x, const month_day_last& y) NOEXCEPT
    {
        return !(x < y);
    }

    namespace detail
    {

        template<class CharT, class Traits>
        std::basic_ostream<CharT, Traits>&
            low_level_fmt(std::basic_ostream<CharT, Traits>& os, const month_day_last& mdl)
        {
            return low_level_fmt(os, mdl.month()) << "/last";
        }

    }  // namespace detail

    template<class CharT, class Traits>
    inline
        std::basic_ostream<CharT, Traits>&
        operator<<(std::basic_ostream<CharT, Traits>& os, const month_day_last& mdl)
    {
        detail::low_level_fmt(os, mdl);
        if (!mdl.ok())
            os << " is not a valid month_day_last";
        return os;
    }

    // month_weekday

    CONSTCD11
        inline
        month_weekday::month_weekday(const date::month& m,
            const date::weekday_indexed& wdi) NOEXCEPT
        : m_(m)
        , wdi_(wdi)
    {}

    CONSTCD11 inline month month_weekday::month() const NOEXCEPT { return m_; }

    CONSTCD11
        inline
        weekday_indexed
        month_weekday::weekday_indexed() const NOEXCEPT
    {
        return wdi_;
    }

    CONSTCD11
        inline
        bool
        month_weekday::ok() const NOEXCEPT
    {
        return m_.ok() && wdi_.ok();
    }

    CONSTCD11
        inline
        bool
        operator==(const month_weekday& x, const month_weekday& y) NOEXCEPT
    {
        return x.month() == y.month() && x.weekday_indexed() == y.weekday_indexed();
    }

    CONSTCD11
        inline
        bool
        operator!=(const month_weekday& x, const month_weekday& y) NOEXCEPT
    {
        return !(x == y);
    }

    namespace detail
    {

        template<class CharT, class Traits>
        std::basic_ostream<CharT, Traits>&
            low_level_fmt(std::basic_ostream<CharT, Traits>& os, const month_weekday& mwd)
        {
            low_level_fmt(os, mwd.month()) << '/';
            return low_level_fmt(os, mwd.weekday_indexed());
        }

    }  // namespace detail

    template<class CharT, class Traits>
    inline
        std::basic_ostream<CharT, Traits>&
        operator<<(std::basic_ostream<CharT, Traits>& os, const month_weekday& mwd)
    {
        detail::low_level_fmt(os, mwd);
        if (!mwd.ok())
            os << " is not a valid month_weekday";
        return os;
    }

    // month_weekday_last

    CONSTCD11
        inline
        month_weekday_last::month_weekday_last(const date::month& m,
            const date::weekday_last& wdl) NOEXCEPT
        : m_(m)
        , wdl_(wdl)
    {}

    CONSTCD11 inline month month_weekday_last::month() const NOEXCEPT { return m_; }

    CONSTCD11
        inline
        weekday_last
        month_weekday_last::weekday_last() const NOEXCEPT
    {
        return wdl_;
    }

    CONSTCD11
        inline
        bool
        month_weekday_last::ok() const NOEXCEPT
    {
        return m_.ok() && wdl_.ok();
    }

    CONSTCD11
        inline
        bool
        operator==(const month_weekday_last& x, const month_weekday_last& y) NOEXCEPT
    {
        return x.month() == y.month() && x.weekday_last() == y.weekday_last();
    }

    CONSTCD11
        inline
        bool
        operator!=(const month_weekday_last& x, const month_weekday_last& y) NOEXCEPT
    {
        return !(x == y);
    }

    namespace detail
    {

        template<class CharT, class Traits>
        std::basic_ostream<CharT, Traits>&
            low_level_fmt(std::basic_ostream<CharT, Traits>& os, const month_weekday_last& mwdl)
        {
            low_level_fmt(os, mwdl.month()) << '/';
            return low_level_fmt(os, mwdl.weekday_last());
        }

    }  // namespace detail

    template<class CharT, class Traits>
    inline
        std::basic_ostream<CharT, Traits>&
        operator<<(std::basic_ostream<CharT, Traits>& os, const month_weekday_last& mwdl)
    {
        detail::low_level_fmt(os, mwdl);
        if (!mwdl.ok())
            os << " is not a valid month_weekday_last";
        return os;
    }

    // year_month_day_last

    CONSTCD11
        inline
        year_month_day_last::year_month_day_last(const date::year& y,
            const date::month_day_last& mdl) NOEXCEPT
        : y_(y)
        , mdl_(mdl)
    {}

    template<class>
    CONSTCD14
        inline
        year_month_day_last&
        year_month_day_last::operator+=(const months& m) NOEXCEPT
    {
        *this = *this + m;
        return *this;
    }

    template<class>
    CONSTCD14
        inline
        year_month_day_last&
        year_month_day_last::operator-=(const months& m) NOEXCEPT
    {
        *this = *this - m;
        return *this;
    }

    CONSTCD14
        inline
        year_month_day_last&
        year_month_day_last::operator+=(const years& y) NOEXCEPT
    {
        *this = *this + y;
        return *this;
    }

    CONSTCD14
        inline
        year_month_day_last&
        year_month_day_last::operator-=(const years& y) NOEXCEPT
    {
        *this = *this - y;
        return *this;
    }

    CONSTCD11 inline year year_month_day_last::year() const NOEXCEPT { return y_; }
    CONSTCD11 inline month year_month_day_last::month() const NOEXCEPT { return mdl_.month(); }

    CONSTCD11
        inline
        month_day_last
        year_month_day_last::month_day_last() const NOEXCEPT
    {
        return mdl_;
    }

    CONSTCD14
        inline
        day
        year_month_day_last::day() const NOEXCEPT
    {
        CONSTDATA date::day d[] =
        {
            date::day(31), date::day(28), date::day(31),
            date::day(30), date::day(31), date::day(30),
            date::day(31), date::day(31), date::day(30),
            date::day(31), date::day(30), date::day(31)
        };
        return (month() != February || !y_.is_leap()) && mdl_.ok() ?
            d[static_cast<unsigned>(month()) - 1] : date::day{ 29 };
    }

    CONSTCD14
        inline
        year_month_day_last::operator sys_days() const NOEXCEPT
    {
        return sys_days(year() / month() / day());
    }

    CONSTCD14
        inline
        year_month_day_last::operator local_days() const NOEXCEPT
    {
        return local_days(year() / month() / day());
    }

    CONSTCD11
        inline
        bool
        year_month_day_last::ok() const NOEXCEPT
    {
        return y_.ok() && mdl_.ok();
    }

    CONSTCD11
        inline
        bool
        operator==(const year_month_day_last& x, const year_month_day_last& y) NOEXCEPT
    {
        return x.year() == y.year() && x.month_day_last() == y.month_day_last();
    }

    CONSTCD11
        inline
        bool
        operator!=(const year_month_day_last& x, const year_month_day_last& y) NOEXCEPT
    {
        return !(x == y);
    }

    CONSTCD11
        inline
        bool
        operator<(const year_month_day_last& x, const year_month_day_last& y) NOEXCEPT
    {
        return x.year() < y.year() ? true
            : (x.year() > y.year() ? false
                : (x.month_day_last() < y.month_day_last()));
    }

    CONSTCD11
        inline
        bool
        operator>(const year_month_day_last& x, const year_month_day_last& y) NOEXCEPT
    {
        return y < x;
    }

    CONSTCD11
        inline
        bool
        operator<=(const year_month_day_last& x, const year_month_day_last& y) NOEXCEPT
    {
        return !(y < x);
    }

    CONSTCD11
        inline
        bool
        operator>=(const year_month_day_last& x, const year_month_day_last& y) NOEXCEPT
    {
        return !(x < y);
    }

    namespace detail
    {

        template<class CharT, class Traits>
        std::basic_ostream<CharT, Traits>&
            low_level_fmt(std::basic_ostream<CharT, Traits>& os, const year_month_day_last& ymdl)
        {
            low_level_fmt(os, ymdl.year()) << '/';
            return low_level_fmt(os, ymdl.month_day_last());
        }

    }  // namespace detail

    template<class CharT, class Traits>
    inline
        std::basic_ostream<CharT, Traits>&
        operator<<(std::basic_ostream<CharT, Traits>& os, const year_month_day_last& ymdl)
    {
        detail::low_level_fmt(os, ymdl);
        if (!ymdl.ok())
            os << " is not a valid year_month_day_last";
        return os;
    }

    template<class>
    CONSTCD14
        inline
        year_month_day_last
        operator+(const year_month_day_last& ymdl, const months& dm) NOEXCEPT
    {
        return (ymdl.year() / ymdl.month() + dm) / last;
    }

    template<class>
    CONSTCD14
        inline
        year_month_day_last
        operator+(const months& dm, const year_month_day_last& ymdl) NOEXCEPT
    {
        return ymdl + dm;
    }

    template<class>
    CONSTCD14
        inline
        year_month_day_last
        operator-(const year_month_day_last& ymdl, const months& dm) NOEXCEPT
    {
        return ymdl + (-dm);
    }

    CONSTCD11
        inline
        year_month_day_last
        operator+(const year_month_day_last& ymdl, const years& dy) NOEXCEPT
    {
        return { ymdl.year() + dy, ymdl.month_day_last() };
    }

    CONSTCD11
        inline
        year_month_day_last
        operator+(const years& dy, const year_month_day_last& ymdl) NOEXCEPT
    {
        return ymdl + dy;
    }

    CONSTCD11
        inline
        year_month_day_last
        operator-(const year_month_day_last& ymdl, const years& dy) NOEXCEPT
    {
        return ymdl + (-dy);
    }

    // year_month_day

    CONSTCD11
        inline
        year_month_day::year_month_day(const date::year& y, const date::month& m,
            const date::day& d) NOEXCEPT
        : y_(y)
        , m_(m)
        , d_(d)
    {}

    CONSTCD14
        inline
        year_month_day::year_month_day(const year_month_day_last& ymdl) NOEXCEPT
        : y_(ymdl.year())
        , m_(ymdl.month())
        , d_(ymdl.day())
    {}

    CONSTCD14
        inline
        year_month_day::year_month_day(sys_days dp) NOEXCEPT
        : year_month_day(from_days(dp.time_since_epoch()))
    {}

    CONSTCD14
        inline
        year_month_day::year_month_day(local_days dp) NOEXCEPT
        : year_month_day(from_days(dp.time_since_epoch()))
    {}

    CONSTCD11 inline year year_month_day::year() const NOEXCEPT { return y_; }
    CONSTCD11 inline month year_month_day::month() const NOEXCEPT { return m_; }
    CONSTCD11 inline day year_month_day::day() const NOEXCEPT { return d_; }

    template<class>
    CONSTCD14
        inline
        year_month_day&
        year_month_day::operator+=(const months& m) NOEXCEPT
    {
        *this = *this + m;
        return *this;
    }

    template<class>
    CONSTCD14
        inline
        year_month_day&
        year_month_day::operator-=(const months& m) NOEXCEPT
    {
        *this = *this - m;
        return *this;
    }

    CONSTCD14
        inline
        year_month_day&
        year_month_day::operator+=(const years& y) NOEXCEPT
    {
        *this = *this + y;
        return *this;
    }

    CONSTCD14
        inline
        year_month_day&
        year_month_day::operator-=(const years& y) NOEXCEPT
    {
        *this = *this - y;
        return *this;
    }

    CONSTCD14
        inline
        days
        year_month_day::to_days() const NOEXCEPT
    {
        static_assert(std::numeric_limits<unsigned>::digits >= 18,
            "This algorithm has not been ported to a 16 bit unsigned integer");
        static_assert(std::numeric_limits<int>::digits >= 20,
            "This algorithm has not been ported to a 16 bit signed integer");
        auto const y = static_cast<int>(y_) - (m_ <= February);
        auto const m = static_cast<unsigned>(m_);
        auto const d = static_cast<unsigned>(d_);
        auto const era = (y >= 0 ? y : y - 399) / 400;
        auto const yoe = static_cast<unsigned>(y - era * 400);       // [0, 399]
        auto const doy = (153 * (m > 2 ? m - 3 : m + 9) + 2) / 5 + d - 1;      // [0, 365]
        auto const doe = yoe * 365 + yoe / 4 - yoe / 100 + doy;          // [0, 146096]
        return days{ era * 146097 + static_cast<int>(doe) - 719468 };
    }

    CONSTCD14
        inline
        year_month_day::operator sys_days() const NOEXCEPT
    {
        return sys_days{ to_days() };
    }

    CONSTCD14
        inline
        year_month_day::operator local_days() const NOEXCEPT
    {
        return local_days{ to_days() };
    }

    CONSTCD14
        inline
        bool
        year_month_day::ok() const NOEXCEPT
    {
        if (!(y_.ok() && m_.ok()))
            return false;
        return date::day{ 1 } <= d_ && d_ <= (y_ / m_ / last).day();
    }

    CONSTCD11
        inline
        bool
        operator==(const year_month_day& x, const year_month_day& y) NOEXCEPT
    {
        return x.year() == y.year() && x.month() == y.month() && x.day() == y.day();
    }

    CONSTCD11
        inline
        bool
        operator!=(const year_month_day& x, const year_month_day& y) NOEXCEPT
    {
        return !(x == y);
    }

    CONSTCD11
        inline
        bool
        operator<(const year_month_day& x, const year_month_day& y) NOEXCEPT
    {
        return x.year() < y.year() ? true
            : (x.year() > y.year() ? false
                : (x.month() < y.month() ? true
                    : (x.month() > y.month() ? false
                        : (x.day() < y.day()))));
    }

    CONSTCD11
        inline
        bool
        operator>(const year_month_day& x, const year_month_day& y) NOEXCEPT
    {
        return y < x;
    }

    CONSTCD11
        inline
        bool
        operator<=(const year_month_day& x, const year_month_day& y) NOEXCEPT
    {
        return !(y < x);
    }

    CONSTCD11
        inline
        bool
        operator>=(const year_month_day& x, const year_month_day& y) NOEXCEPT
    {
        return !(x < y);
    }

    template<class CharT, class Traits>
    inline
        std::basic_ostream<CharT, Traits>&
        operator<<(std::basic_ostream<CharT, Traits>& os, const year_month_day& ymd)
    {
        detail::save_ostream<CharT, Traits> _(os);
        os.fill('0');
        os.flags(std::ios::dec | std::ios::right);
        os.imbue(std::locale::classic());
        os << static_cast<int>(ymd.year()) << '-';
        os.width(2);
        os << static_cast<unsigned>(ymd.month()) << '-';
        os.width(2);
        os << static_cast<unsigned>(ymd.day());
        if (!ymd.ok())
            os << " is not a valid year_month_day";
        return os;
    }

    CONSTCD14
        inline
        year_month_day
        year_month_day::from_days(days dp) NOEXCEPT
    {
        static_assert(std::numeric_limits<unsigned>::digits >= 18,
            "This algorithm has not been ported to a 16 bit unsigned integer");
        static_assert(std::numeric_limits<int>::digits >= 20,
            "This algorithm has not been ported to a 16 bit signed integer");
        auto const z = dp.count() + 719468;
        auto const era = (z >= 0 ? z : z - 146096) / 146097;
        auto const doe = static_cast<unsigned>(z - era * 146097);          // [0, 146096]
        auto const yoe = (doe - doe / 1460 + doe / 36524 - doe / 146096) / 365;  // [0, 399]
        auto const y = static_cast<days::rep>(yoe) + era * 400;
        auto const doy = doe - (365 * yoe + yoe / 4 - yoe / 100);                // [0, 365]
        auto const mp = (5 * doy + 2) / 153;                                   // [0, 11]
        auto const d = doy - (153 * mp + 2) / 5 + 1;                             // [1, 31]
        auto const m = mp < 10 ? mp + 3 : mp - 9;                              // [1, 12]
        return year_month_day{ date::year{y + (m <= 2)}, date::month(m), date::day(d) };
    }

    template<class>
    CONSTCD14
        inline
        year_month_day
        operator+(const year_month_day& ymd, const months& dm) NOEXCEPT
    {
        return (ymd.year() / ymd.month() + dm) / ymd.day();
    }

    template<class>
    CONSTCD14
        inline
        year_month_day
        operator+(const months& dm, const year_month_day& ymd) NOEXCEPT
    {
        return ymd + dm;
    }

    template<class>
    CONSTCD14
        inline
        year_month_day
        operator-(const year_month_day& ymd, const months& dm) NOEXCEPT
    {
        return ymd + (-dm);
    }

    CONSTCD11
        inline
        year_month_day
        operator+(const year_month_day& ymd, const years& dy) NOEXCEPT
    {
        return (ymd.year() + dy) / ymd.month() / ymd.day();
    }

    CONSTCD11
        inline
        year_month_day
        operator+(const years& dy, const year_month_day& ymd) NOEXCEPT
    {
        return ymd + dy;
    }

    CONSTCD11
        inline
        year_month_day
        operator-(const year_month_day& ymd, const years& dy) NOEXCEPT
    {
        return ymd + (-dy);
    }

    // year_month_weekday

    CONSTCD11
        inline
        year_month_weekday::year_month_weekday(const date::year& y, const date::month& m,
            const date::weekday_indexed& wdi)
        NOEXCEPT
        : y_(y)
        , m_(m)
        , wdi_(wdi)
    {}

    CONSTCD14
        inline
        year_month_weekday::year_month_weekday(const sys_days& dp) NOEXCEPT
        : year_month_weekday(from_days(dp.time_since_epoch()))
    {}

    CONSTCD14
        inline
        year_month_weekday::year_month_weekday(const local_days& dp) NOEXCEPT
        : year_month_weekday(from_days(dp.time_since_epoch()))
    {}

    template<class>
    CONSTCD14
        inline
        year_month_weekday&
        year_month_weekday::operator+=(const months& m) NOEXCEPT
    {
        *this = *this + m;
        return *this;
    }

    template<class>
    CONSTCD14
        inline
        year_month_weekday&
        year_month_weekday::operator-=(const months& m) NOEXCEPT
    {
        *this = *this - m;
        return *this;
    }

    CONSTCD14
        inline
        year_month_weekday&
        year_month_weekday::operator+=(const years& y) NOEXCEPT
    {
        *this = *this + y;
        return *this;
    }

    CONSTCD14
        inline
        year_month_weekday&
        year_month_weekday::operator-=(const years& y) NOEXCEPT
    {
        *this = *this - y;
        return *this;
    }

    CONSTCD11 inline year year_month_weekday::year() const NOEXCEPT { return y_; }
    CONSTCD11 inline month year_month_weekday::month() const NOEXCEPT { return m_; }

    CONSTCD11
        inline
        weekday
        year_month_weekday::weekday() const NOEXCEPT
    {
        return wdi_.weekday();
    }

    CONSTCD11
        inline
        unsigned
        year_month_weekday::index() const NOEXCEPT
    {
        return wdi_.index();
    }

    CONSTCD11
        inline
        weekday_indexed
        year_month_weekday::weekday_indexed() const NOEXCEPT
    {
        return wdi_;
    }

    CONSTCD14
        inline
        year_month_weekday::operator sys_days() const NOEXCEPT
    {
        return sys_days{ to_days() };
    }

    CONSTCD14
        inline
        year_month_weekday::operator local_days() const NOEXCEPT
    {
        return local_days{ to_days() };
    }

    CONSTCD14
        inline
        bool
        year_month_weekday::ok() const NOEXCEPT
    {
        if (!y_.ok() || !m_.ok() || !wdi_.weekday().ok() || wdi_.index() < 1)
            return false;
        if (wdi_.index() <= 4)
            return true;
        auto d2 = wdi_.weekday() - date::weekday(static_cast<sys_days>(y_ / m_ / 1)) +
            days((wdi_.index() - 1) * 7 + 1);
        return static_cast<unsigned>(d2.count()) <= static_cast<unsigned>((y_ / m_ / last).day());
    }

    CONSTCD14
        inline
        year_month_weekday
        year_month_weekday::from_days(days d) NOEXCEPT
    {
        sys_days dp{ d };
        auto const wd = date::weekday(dp);
        auto const ymd = year_month_day(dp);
        return { ymd.year(), ymd.month(), wd[(static_cast<unsigned>(ymd.day()) - 1) / 7 + 1] };
    }

    CONSTCD14
        inline
        days
        year_month_weekday::to_days() const NOEXCEPT
    {
        auto d = sys_days(y_ / m_ / 1);
        return (d + (wdi_.weekday() - date::weekday(d) + days{ (wdi_.index() - 1) * 7 })
            ).time_since_epoch();
    }

    CONSTCD11
        inline
        bool
        operator==(const year_month_weekday& x, const year_month_weekday& y) NOEXCEPT
    {
        return x.year() == y.year() && x.month() == y.month() &&
            x.weekday_indexed() == y.weekday_indexed();
    }

    CONSTCD11
        inline
        bool
        operator!=(const year_month_weekday& x, const year_month_weekday& y) NOEXCEPT
    {
        return !(x == y);
    }

    template<class CharT, class Traits>
    inline
        std::basic_ostream<CharT, Traits>&
        operator<<(std::basic_ostream<CharT, Traits>& os, const year_month_weekday& ymwdi)
    {
        detail::low_level_fmt(os, ymwdi.year()) << '/';
        detail::low_level_fmt(os, ymwdi.month()) << '/';
        detail::low_level_fmt(os, ymwdi.weekday_indexed());
        if (!ymwdi.ok())
            os << " is not a valid year_month_weekday";
        return os;
    }

    template<class>
    CONSTCD14
        inline
        year_month_weekday
        operator+(const year_month_weekday& ymwd, const months& dm) NOEXCEPT
    {
        return (ymwd.year() / ymwd.month() + dm) / ymwd.weekday_indexed();
    }

    template<class>
    CONSTCD14
        inline
        year_month_weekday
        operator+(const months& dm, const year_month_weekday& ymwd) NOEXCEPT
    {
        return ymwd + dm;
    }

    template<class>
    CONSTCD14
        inline
        year_month_weekday
        operator-(const year_month_weekday& ymwd, const months& dm) NOEXCEPT
    {
        return ymwd + (-dm);
    }

    CONSTCD11
        inline
        year_month_weekday
        operator+(const year_month_weekday& ymwd, const years& dy) NOEXCEPT
    {
        return { ymwd.year() + dy, ymwd.month(), ymwd.weekday_indexed() };
    }

    CONSTCD11
        inline
        year_month_weekday
        operator+(const years& dy, const year_month_weekday& ymwd) NOEXCEPT
    {
        return ymwd + dy;
    }

    CONSTCD11
        inline
        year_month_weekday
        operator-(const year_month_weekday& ymwd, const years& dy) NOEXCEPT
    {
        return ymwd + (-dy);
    }

    // year_month_weekday_last

    CONSTCD11
        inline
        year_month_weekday_last::year_month_weekday_last(const date::year& y,
            const date::month& m,
            const date::weekday_last& wdl) NOEXCEPT
        : y_(y)
        , m_(m)
        , wdl_(wdl)
    {}

    template<class>
    CONSTCD14
        inline
        year_month_weekday_last&
        year_month_weekday_last::operator+=(const months& m) NOEXCEPT
    {
        *this = *this + m;
        return *this;
    }

    template<class>
    CONSTCD14
        inline
        year_month_weekday_last&
        year_month_weekday_last::operator-=(const months& m) NOEXCEPT
    {
        *this = *this - m;
        return *this;
    }

    CONSTCD14
        inline
        year_month_weekday_last&
        year_month_weekday_last::operator+=(const years& y) NOEXCEPT
    {
        *this = *this + y;
        return *this;
    }

    CONSTCD14
        inline
        year_month_weekday_last&
        year_month_weekday_last::operator-=(const years& y) NOEXCEPT
    {
        *this = *this - y;
        return *this;
    }

    CONSTCD11 inline year year_month_weekday_last::year() const NOEXCEPT { return y_; }
    CONSTCD11 inline month year_month_weekday_last::month() const NOEXCEPT { return m_; }

    CONSTCD11
        inline
        weekday
        year_month_weekday_last::weekday() const NOEXCEPT
    {
        return wdl_.weekday();
    }

    CONSTCD11
        inline
        weekday_last
        year_month_weekday_last::weekday_last() const NOEXCEPT
    {
        return wdl_;
    }

    CONSTCD14
        inline
        year_month_weekday_last::operator sys_days() const NOEXCEPT
    {
        return sys_days{ to_days() };
    }

    CONSTCD14
        inline
        year_month_weekday_last::operator local_days() const NOEXCEPT
    {
        return local_days{ to_days() };
    }

    CONSTCD11
        inline
        bool
        year_month_weekday_last::ok() const NOEXCEPT
    {
        return y_.ok() && m_.ok() && wdl_.ok();
    }

    CONSTCD14
        inline
        days
        year_month_weekday_last::to_days() const NOEXCEPT
    {
        auto const d = sys_days(y_ / m_ / last);
        return (d - (date::weekday{ d } - wdl_.weekday())).time_since_epoch();
    }

    CONSTCD11
        inline
        bool
        operator==(const year_month_weekday_last& x, const year_month_weekday_last& y) NOEXCEPT
    {
        return x.year() == y.year() && x.month() == y.month() &&
            x.weekday_last() == y.weekday_last();
    }

    CONSTCD11
        inline
        bool
        operator!=(const year_month_weekday_last& x, const year_month_weekday_last& y) NOEXCEPT
    {
        return !(x == y);
    }

    template<class CharT, class Traits>
    inline
        std::basic_ostream<CharT, Traits>&
        operator<<(std::basic_ostream<CharT, Traits>& os, const year_month_weekday_last& ymwdl)
    {
        detail::low_level_fmt(os, ymwdl.year()) << '/';
        detail::low_level_fmt(os, ymwdl.month()) << '/';
        detail::low_level_fmt(os, ymwdl.weekday_last());
        if (!ymwdl.ok())
            os << " is not a valid year_month_weekday_last";
        return os;
    }

    template<class>
    CONSTCD14
        inline
        year_month_weekday_last
        operator+(const year_month_weekday_last& ymwdl, const months& dm) NOEXCEPT
    {
        return (ymwdl.year() / ymwdl.month() + dm) / ymwdl.weekday_last();
    }

    template<class>
    CONSTCD14
        inline
        year_month_weekday_last
        operator+(const months& dm, const year_month_weekday_last& ymwdl) NOEXCEPT
    {
        return ymwdl + dm;
    }

    template<class>
    CONSTCD14
        inline
        year_month_weekday_last
        operator-(const year_month_weekday_last& ymwdl, const months& dm) NOEXCEPT
    {
        return ymwdl + (-dm);
    }

    CONSTCD11
        inline
        year_month_weekday_last
        operator+(const year_month_weekday_last& ymwdl, const years& dy) NOEXCEPT
    {
        return { ymwdl.year() + dy, ymwdl.month(), ymwdl.weekday_last() };
    }

    CONSTCD11
        inline
        year_month_weekday_last
        operator+(const years& dy, const year_month_weekday_last& ymwdl) NOEXCEPT
    {
        return ymwdl + dy;
    }

    CONSTCD11
        inline
        year_month_weekday_last
        operator-(const year_month_weekday_last& ymwdl, const years& dy) NOEXCEPT
    {
        return ymwdl + (-dy);
    }

    // year_month from operator/()

    CONSTCD11
        inline
        year_month
        operator/(const year& y, const month& m) NOEXCEPT
    {
        return { y, m };
    }

    CONSTCD11
        inline
        year_month
        operator/(const year& y, int   m) NOEXCEPT
    {
        return y / month(static_cast<unsigned>(m));
    }

    // month_day from operator/()

    CONSTCD11
        inline
        month_day
        operator/(const month& m, const day& d) NOEXCEPT
    {
        return { m, d };
    }

    CONSTCD11
        inline
        month_day
        operator/(const day& d, const month& m) NOEXCEPT
    {
        return m / d;
    }

    CONSTCD11
        inline
        month_day
        operator/(const month& m, int d) NOEXCEPT
    {
        return m / day(static_cast<unsigned>(d));
    }

    CONSTCD11
        inline
        month_day
        operator/(int m, const day& d) NOEXCEPT
    {
        return month(static_cast<unsigned>(m)) / d;
    }

    CONSTCD11 inline month_day operator/(const day& d, int m) NOEXCEPT { return m / d; }

    // month_day_last from operator/()

    CONSTCD11
        inline
        month_day_last
        operator/(const month& m, last_spec) NOEXCEPT
    {
        return month_day_last{ m };
    }

    CONSTCD11
        inline
        month_day_last
        operator/(last_spec, const month& m) NOEXCEPT
    {
        return m / last;
    }

    CONSTCD11
        inline
        month_day_last
        operator/(int m, last_spec) NOEXCEPT
    {
        return month(static_cast<unsigned>(m)) / last;
    }

    CONSTCD11
        inline
        month_day_last
        operator/(last_spec, int m) NOEXCEPT
    {
        return m / last;
    }

    // month_weekday from operator/()

    CONSTCD11
        inline
        month_weekday
        operator/(const month& m, const weekday_indexed& wdi) NOEXCEPT
    {
        return { m, wdi };
    }

    CONSTCD11
        inline
        month_weekday
        operator/(const weekday_indexed& wdi, const month& m) NOEXCEPT
    {
        return m / wdi;
    }

    CONSTCD11
        inline
        month_weekday
        operator/(int m, const weekday_indexed& wdi) NOEXCEPT
    {
        return month(static_cast<unsigned>(m)) / wdi;
    }

    CONSTCD11
        inline
        month_weekday
        operator/(const weekday_indexed& wdi, int m) NOEXCEPT
    {
        return m / wdi;
    }

    // month_weekday_last from operator/()

    CONSTCD11
        inline
        month_weekday_last
        operator/(const month& m, const weekday_last& wdl) NOEXCEPT
    {
        return { m, wdl };
    }

    CONSTCD11
        inline
        month_weekday_last
        operator/(const weekday_last& wdl, const month& m) NOEXCEPT
    {
        return m / wdl;
    }

    CONSTCD11
        inline
        month_weekday_last
        operator/(int m, const weekday_last& wdl) NOEXCEPT
    {
        return month(static_cast<unsigned>(m)) / wdl;
    }

    CONSTCD11
        inline
        month_weekday_last
        operator/(const weekday_last& wdl, int m) NOEXCEPT
    {
        return m / wdl;
    }

    // year_month_day from operator/()

    CONSTCD11
        inline
        year_month_day
        operator/(const year_month& ym, const day& d) NOEXCEPT
    {
        return { ym.year(), ym.month(), d };
    }

    CONSTCD11
        inline
        year_month_day
        operator/(const year_month& ym, int d)  NOEXCEPT
    {
        return ym / day(static_cast<unsigned>(d));
    }

    CONSTCD11
        inline
        year_month_day
        operator/(const year& y, const month_day& md) NOEXCEPT
    {
        return y / md.month() / md.day();
    }

    CONSTCD11
        inline
        year_month_day
        operator/(int y, const month_day& md) NOEXCEPT
    {
        return year(y) / md;
    }

    CONSTCD11
        inline
        year_month_day
        operator/(const month_day& md, const year& y)  NOEXCEPT
    {
        return y / md;
    }

    CONSTCD11
        inline
        year_month_day
        operator/(const month_day& md, int y) NOEXCEPT
    {
        return year(y) / md;
    }

    // year_month_day_last from operator/()

    CONSTCD11
        inline
        year_month_day_last
        operator/(const year_month& ym, last_spec) NOEXCEPT
    {
        return { ym.year(), month_day_last{ym.month()} };
    }

    CONSTCD11
        inline
        year_month_day_last
        operator/(const year& y, const month_day_last& mdl) NOEXCEPT
    {
        return { y, mdl };
    }

    CONSTCD11
        inline
        year_month_day_last
        operator/(int y, const month_day_last& mdl) NOEXCEPT
    {
        return year(y) / mdl;
    }

    CONSTCD11
        inline
        year_month_day_last
        operator/(const month_day_last& mdl, const year& y) NOEXCEPT
    {
        return y / mdl;
    }

    CONSTCD11
        inline
        year_month_day_last
        operator/(const month_day_last& mdl, int y) NOEXCEPT
    {
        return year(y) / mdl;
    }

    // year_month_weekday from operator/()

    CONSTCD11
        inline
        year_month_weekday
        operator/(const year_month& ym, const weekday_indexed& wdi) NOEXCEPT
    {
        return { ym.year(), ym.month(), wdi };
    }

    CONSTCD11
        inline
        year_month_weekday
        operator/(const year& y, const month_weekday& mwd) NOEXCEPT
    {
        return { y, mwd.month(), mwd.weekday_indexed() };
    }

    CONSTCD11
        inline
        year_month_weekday
        operator/(int y, const month_weekday& mwd) NOEXCEPT
    {
        return year(y) / mwd;
    }

    CONSTCD11
        inline
        year_month_weekday
        operator/(const month_weekday& mwd, const year& y) NOEXCEPT
    {
        return y / mwd;
    }

    CONSTCD11
        inline
        year_month_weekday
        operator/(const month_weekday& mwd, int y) NOEXCEPT
    {
        return year(y) / mwd;
    }

    // year_month_weekday_last from operator/()

    CONSTCD11
        inline
        year_month_weekday_last
        operator/(const year_month& ym, const weekday_last& wdl) NOEXCEPT
    {
        return { ym.year(), ym.month(), wdl };
    }

    CONSTCD11
        inline
        year_month_weekday_last
        operator/(const year& y, const month_weekday_last& mwdl) NOEXCEPT
    {
        return { y, mwdl.month(), mwdl.weekday_last() };
    }

    CONSTCD11
        inline
        year_month_weekday_last
        operator/(int y, const month_weekday_last& mwdl) NOEXCEPT
    {
        return year(y) / mwdl;
    }

    CONSTCD11
        inline
        year_month_weekday_last
        operator/(const month_weekday_last& mwdl, const year& y) NOEXCEPT
    {
        return y / mwdl;
    }

    CONSTCD11
        inline
        year_month_weekday_last
        operator/(const month_weekday_last& mwdl, int y) NOEXCEPT
    {
        return year(y) / mwdl;
    }

    template <class Duration>
    struct fields;

    template <class CharT, class Traits, class Duration>
    std::basic_ostream<CharT, Traits>&
        to_stream(std::basic_ostream<CharT, Traits>& os, const CharT* fmt,
            const fields<Duration>& fds, const std::string* abbrev = nullptr,
            const std::chrono::seconds* offset_sec = nullptr);

    template <class CharT, class Traits, class Duration, class Alloc>
    std::basic_istream<CharT, Traits>&
        from_stream(std::basic_istream<CharT, Traits>& is, const CharT* fmt,
            fields<Duration>& fds, std::basic_string<CharT, Traits, Alloc>* abbrev = nullptr,
            std::chrono::minutes* offset = nullptr);

    // hh_mm_ss

    namespace detail
    {

        struct undocumented { explicit undocumented() = default; };

        // width<n>::value is the number of fractional decimal digits in 1/n
        // width<0>::value and width<1>::value are defined to be 0
        // If 1/n takes more than 18 fractional decimal digits,
        //   the result is truncated to 19.
        // Example:  width<2>::value    ==  1
        // Example:  width<3>::value    == 19
        // Example:  width<4>::value    ==  2
        // Example:  width<10>::value   ==  1
        // Example:  width<1000>::value ==  3
        template <std::uint64_t n, std::uint64_t d, unsigned w = 0,
            bool should_continue = n % d != 0 && (w < 19)>
            struct width
        {
            static_assert(d > 0, "width called with zero denominator");
            static CONSTDATA unsigned value = 1 + width<n% d * 10, d, w + 1>::value;
        };

        template <std::uint64_t n, std::uint64_t d, unsigned w>
        struct width<n, d, w, false>
        {
            static CONSTDATA unsigned value = 0;
        };

        template <unsigned exp>
        struct static_pow10
        {
        private:
            static CONSTDATA std::uint64_t h = static_pow10<exp / 2>::value;
        public:
            static CONSTDATA std::uint64_t value = h * h * (exp % 2 ? 10 : 1);
        };

        template <>
        struct static_pow10<0>
        {
            static CONSTDATA std::uint64_t value = 1;
        };

        template <class Duration>
        class decimal_format_seconds
        {
            using CT = typename std::common_type<Duration, std::chrono::seconds>::type;
            using rep = typename CT::rep;
            static unsigned CONSTDATA trial_width =
                detail::width<CT::period::num, CT::period::den>::value;
        public:
            static unsigned CONSTDATA width = trial_width < 19 ? trial_width : 6u;
            using precision = std::chrono::duration<rep,
                std::ratio<1, static_pow10<width>::value>>;

        private:
            std::chrono::seconds s_;
            precision            sub_s_;

        public:
            CONSTCD11 decimal_format_seconds()
                : s_()
                , sub_s_()
            {}

            CONSTCD11 explicit decimal_format_seconds(const Duration& d) NOEXCEPT
                : s_(std::chrono::duration_cast<std::chrono::seconds>(d))
                , sub_s_(std::chrono::duration_cast<precision>(d - s_))
            {}

            CONSTCD14 std::chrono::seconds& seconds() NOEXCEPT { return s_; }
            CONSTCD11 std::chrono::seconds seconds() const NOEXCEPT { return s_; }
            CONSTCD11 precision subseconds() const NOEXCEPT { return sub_s_; }

            CONSTCD14 precision to_duration() const NOEXCEPT
            {
                return s_ + sub_s_;
            }

            CONSTCD11 bool in_conventional_range() const NOEXCEPT
            {
                return sub_s_ < std::chrono::seconds{ 1 }&& s_ < std::chrono::minutes{ 1 };
            }

            template <class CharT, class Traits>
            friend
                std::basic_ostream<CharT, Traits>&
                operator<<(std::basic_ostream<CharT, Traits>& os, const decimal_format_seconds& x)
            {
                return x.print(os, std::chrono::treat_as_floating_point<rep>{});
            }

            template <class CharT, class Traits>
            std::basic_ostream<CharT, Traits>&
                print(std::basic_ostream<CharT, Traits>& os, std::true_type) const
            {
                date::detail::save_ostream<CharT, Traits> _(os);
                std::chrono::duration<rep> d = s_ + sub_s_;
                if (d < std::chrono::seconds{ 10 })
                    os << '0';
                os.precision(width + 6);
                os << std::fixed << d.count();
                return os;
            }

            template <class CharT, class Traits>
            std::basic_ostream<CharT, Traits>&
                print(std::basic_ostream<CharT, Traits>& os, std::false_type) const
            {
                date::detail::save_ostream<CharT, Traits> _(os);
                os.fill('0');
                os.flags(std::ios::dec | std::ios::right);
                os.width(2);
                os << s_.count();
                if (width > 0)
                {
#if !ONLY_C_LOCALE
                    os << std::use_facet<std::numpunct<CharT>>(os.getloc()).decimal_point();
#else
                    os << '.';
#endif
                    date::detail::save_ostream<CharT, Traits> _s(os);
                    os.imbue(std::locale::classic());
                    os.width(width);
                    os << sub_s_.count();
                }
                return os;
            }
        };

        template <class Rep, class Period>
        inline
            CONSTCD11
            typename std::enable_if
            <
            std::numeric_limits<Rep>::is_signed,
            std::chrono::duration<Rep, Period>
            >::type
            date_abs(std::chrono::duration<Rep, Period> d)
        {
            return d >= d.zero() ? +d : -d;
        }

        template <class Rep, class Period>
        inline
            CONSTCD11
            typename std::enable_if
            <
            !std::numeric_limits<Rep>::is_signed,
            std::chrono::duration<Rep, Period>
            >::type
            date_abs(std::chrono::duration<Rep, Period> d)
        {
            return d;
        }

    }  // namespace detail

    template <class Duration>
    class hh_mm_ss
    {
        using dfs = detail::decimal_format_seconds<typename std::common_type<Duration,
            std::chrono::seconds>::type>;

        std::chrono::hours h_;
        std::chrono::minutes m_;
        dfs s_;
        bool neg_;

    public:
        static unsigned CONSTDATA fractional_width = dfs::width;
        using precision = typename dfs::precision;

        CONSTCD11 hh_mm_ss() NOEXCEPT
            : hh_mm_ss(Duration::zero())
        {}

        CONSTCD11 explicit hh_mm_ss(Duration d) NOEXCEPT
            : h_(std::chrono::duration_cast<std::chrono::hours>(detail::date_abs(d)))
            , m_(std::chrono::duration_cast<std::chrono::minutes>(detail::date_abs(d)) - h_)
            , s_(detail::date_abs(d) - h_ - m_)
            , neg_(d < Duration::zero())
        {}

        CONSTCD11 std::chrono::hours hours() const NOEXCEPT { return h_; }
        CONSTCD11 std::chrono::minutes minutes() const NOEXCEPT { return m_; }
        CONSTCD11 std::chrono::seconds seconds() const NOEXCEPT { return s_.seconds(); }
        CONSTCD14 std::chrono::seconds&
            seconds(detail::undocumented) NOEXCEPT { return s_.seconds(); }
        CONSTCD11 precision subseconds() const NOEXCEPT { return s_.subseconds(); }
        CONSTCD11 bool is_negative() const NOEXCEPT { return neg_; }

        CONSTCD11 explicit operator precision()   const NOEXCEPT { return to_duration(); }
        CONSTCD11          precision to_duration() const NOEXCEPT
        {
            return (s_.to_duration() + m_ + h_) * (1 - 2 * neg_);
        }

        CONSTCD11 bool in_conventional_range() const NOEXCEPT
        {
            return !neg_ && h_ < days{ 1 }&& m_ < std::chrono::hours{ 1 }&&
                s_.in_conventional_range();
        }

    private:

        template <class charT, class traits>
        friend
            std::basic_ostream<charT, traits>&
            operator<<(std::basic_ostream<charT, traits>& os, hh_mm_ss const& tod)
        {
            if (tod.is_negative())
                os << '-';
            if (tod.h_ < std::chrono::hours{ 10 })
                os << '0';
            os << tod.h_.count() << ':';
            if (tod.m_ < std::chrono::minutes{ 10 })
                os << '0';
            os << tod.m_.count() << ':' << tod.s_;
            return os;
        }

        template <class CharT, class Traits, class Duration2>
        friend
            std::basic_ostream<CharT, Traits>&
            date::to_stream(std::basic_ostream<CharT, Traits>& os, const CharT* fmt,
                const fields<Duration2>& fds, const std::string* abbrev,
                const std::chrono::seconds* offset_sec);

        template <class CharT, class Traits, class Duration2, class Alloc>
        friend
            std::basic_istream<CharT, Traits>&
            date::from_stream(std::basic_istream<CharT, Traits>& is, const CharT* fmt,
                fields<Duration2>& fds,
                std::basic_string<CharT, Traits, Alloc>* abbrev, std::chrono::minutes* offset);
    };

    inline
        CONSTCD14
        bool
        is_am(std::chrono::hours const& h) NOEXCEPT
    {
        using std::chrono::hours;
        return hours{ 0 } <= h && h < hours{ 12 };
    }

    inline
        CONSTCD14
        bool
        is_pm(std::chrono::hours const& h) NOEXCEPT
    {
        using std::chrono::hours;
        return hours{ 12 } <= h && h < hours{ 24 };
    }

    inline
        CONSTCD14
        std::chrono::hours
        make12(std::chrono::hours h) NOEXCEPT
    {
        using std::chrono::hours;
        if (h < hours{ 12 })
        {
            if (h == hours{ 0 })
                h = hours{ 12 };
        }
        else
        {
            if (h != hours{ 12 })
                h = h - hours{ 12 };
        }
        return h;
    }

    inline
        CONSTCD14
        std::chrono::hours
        make24(std::chrono::hours h, bool is_pm) NOEXCEPT
    {
        using std::chrono::hours;
        if (is_pm)
        {
            if (h != hours{ 12 })
                h = h + hours{ 12 };
        }
        else if (h == hours{ 12 })
            h = hours{ 0 };
        return h;
    }

    template <class Duration>
    using time_of_day = hh_mm_ss<Duration>;

    template <class Rep, class Period>
    CONSTCD11
        inline
        hh_mm_ss<std::chrono::duration<Rep, Period>>
        make_time(const std::chrono::duration<Rep, Period>& d)
    {
        return hh_mm_ss<std::chrono::duration<Rep, Period>>(d);
    }
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
