guidosch/bikecounter/software/BikeCounterPro/src/timerSchedule/timerSchedule.hpp

#ifndef TIMERSCHEDULE_H
#define TIMERSCHEDULE_H

#include <chrono>
#include <stdint.h>
#include "date.h"

class TimerSchedule
{
public:
    std::chrono::time_point<std::chrono::system_clock, std::chrono::seconds> getNextIntervalTime(std::chrono::time_point<std::chrono::system_clock, std::chrono::seconds> currentDateTime);
    uint32_t getCurrentIntervalSeconds(std::chrono::time_point<std::chrono::system_clock, std::chrono::seconds> currentDateTime);
    uint32_t getCurrentIntervalMinutes(std::chrono::time_point<std::chrono::system_clock, std::chrono::seconds> currentDateTime);

private:
    static const int intervalCount = 3;
    // TimeSpan timeSpanIntervals[intervalCount] = {TimeSpan(0, 6, 0, 0), TimeSpan(0, 2, 0, 0), TimeSpan(0, 6, 0, 0)}; // {dayInterval, nightInterval}
    uint32_t timeSpanIntervals[intervalCount] = {uint32_t(6 * 60 * 60), uint32_t(2 * 60 * 60), uint32_t(6 * 60 * 60)}; // seconds
    int IntervalStartUTC[intervalCount][12] = {
        {0, 0, 0, 0, 0, 0, 0, 0, 0, 0, 0, 0},
        {7, 6, 5, 5, 5, 5, 5, 5, 6, 6, 6, 7},              // ZRH (+1) { 8,  7,  6,  6,  6,  6,  6,  6,  7,  7,  7,  8} start day interval
        {16, 17, 19, 20, 21, 21, 21, 20, 19, 18, 16, 16}}; // ZRH (+1) {17, 18, 20, 21, 22, 22, 22, 21, 20, 19, 17, 17} start night interval
    bool isLastCall = false;
    int getIntervalId(int currentHour, int currentMonth);
};

#endif // TIMERSCHEDULE_H
