guidosch/bikecounter/software/BikeCounterPro/src/HAL/hal_arduino.hpp

#ifndef HAL_ARDUINO_H
#define HAL_ARDUINO_H

#include "hal_interface.hpp"
#include <string>
#include <RTCZero.h>
#include <Adafruit_AM2320.h>
#include <ArduinoLowPower.h>
#include <SPI.h>
#include <SparkFun_SPI_SerialFlash.h>
#include <MKRWAN.h>

class HAL_Arduino : public HAL
{
public:
    // Singletons should not be cloneable and not be assignable.
    HAL_Arduino(HAL_Arduino &other) = delete;
    void operator=(const HAL_Arduino &) = delete;

    static HAL_Arduino *getInstance();

    virtual void rtcBegin(bool resetTime = false) { rtc.begin(true); }
    virtual void rtcSetEpoch(uint32_t ts) { rtc.setEpoch(ts); }
    virtual uint32_t rtcGetEpoch() { return rtc.getEpoch(); }
    virtual uint8_t rtcGetHours() { return rtc.getHours(); }
    virtual uint8_t rtcGetMinutes() { return rtc.getMinutes(); }
    virtual uint8_t rtcGetSeconds() { return rtc.getSeconds(); }
    virtual uint8_t rtcGetDay() { return rtc.getDay(); }
    virtual uint8_t rtcGetMonth() { return rtc.getMonth(); }
    virtual uint8_t rtcGetYear() { return rtc.getYear(); }

    virtual void I2CInit() { Wire.begin(); }

    virtual void AM2320Init() { am2320.begin(); }
    virtual float AM2320ReadTemperature() { return am2320.readTemperature(); }
    virtual float AM2320ReadHumidity() { return am2320.readHumidity(); }

    virtual bool getEuiAndKeyFromFlash(std::string *appEui, std::string *appKey);

    virtual unsigned long getMillis() { return Arduino_h::millis(); }
    virtual void waitHere(unsigned long ms) { Arduino_h::delay(ms); };

    virtual int LoRaAvailable() { return modem.available(); }
    virtual bool LoRaBegin() { return modem.begin(EU868); }
    virtual std::string LoRaVersion() { return modem.version().c_str(); }
    virtual std::string LoRaDeviceEUI() { return modem.deviceEUI().c_str(); }
    virtual int LoRaRead() { return modem.read(); }
    virtual bool LoRaRestart() { return modem.restart(); }
    virtual int LoRaJoinOTAA(std::string eui, std::string key) { return modem.joinOTAA(eui.c_str(), key.c_str()); }
    virtual void LoRaSetMinPollInterval(unsigned long secs) { modem.minPollInterval(secs); }
    virtual void LoRaBeginPacket() { modem.beginPacket(); }
    virtual size_t LoRaWrite(const uint8_t *msgBuffer, size_t msgSize) { return modem.write(msgBuffer, msgSize); }
    virtual int LoRaEndPacket(bool confirmed) { return modem.endPacket(confirmed); }

    virtual void SerialBeginAndWait(unsigned long baudrate)
    {
        Serial.begin(baudrate);
        while (!Serial)
            ;
    }
    virtual size_t SerialPrintLn(std::string msg) { return Serial.println(msg.c_str()); }

    virtual void digitalWrite(uint8_t pinNumber, unsigned int value) { Arduino_h::digitalWrite(pinNumber, static_cast<PinStatus>(value)); }
    virtual int digitalRead(uint8_t pinNumber) { return Arduino_h::digitalRead(pinNumber); }
    virtual void pinMode(uint8_t pinNumber, GPIOPinMode pinMode) { Arduino_h::pinMode(pinNumber, static_cast<PinMode>(pinMode)); }
    virtual void setAnalogReference() { Arduino_h::analogReference(AR_DEFAULT); } // The MKR WAN 1310 3.3V reference voltage for battery measurements
    virtual void analogWrite(uint8_t pinNumber, int value) { Arduino_h::analogWrite(pinNumber, value); }
    virtual int analogRead(uint8_t pinNumber) { return Arduino_h::analogRead(pinNumber); }

    virtual void attachInterruptWakeup(uint32_t pin, void (*callback)(void), TriggerMode mode) { LowPower.attachInterruptWakeup(digitalPinToInterrupt(pin), callback, static_cast<PinStatus>(mode)); };
    virtual void deepSleep(int ms) { LowPower.deepSleep(ms); }

protected:
    HAL_Arduino()
    {
    }
    ~HAL_Arduino() {}

private:
    static HAL_Arduino *instance;
    // Thread-save Singleton (not needed for Arduino)
    // static std::mutex mutex_;

    // Internal RTC object
    RTCZero rtc;

    // Humidity and temperature sensor object
    Adafruit_AM2320 am2320 = Adafruit_AM2320();

    // SPI serial flash parameter
    const byte PIN_FLASH_CS = 32;
    // SPI serial flash object
    SFE_SPI_FLASH flash;

    // LoRa modem object
    LoRaModem modem = LoRaModem(Serial1);
};

#endif // HAL_ARDUINO_H
